kylebsmith/ESP32-S3-RLCD-cYbErDeCk/docs/DATUMS.md

# Dimensional datum sheet

Every dimension this enclosure is built from, with its provenance, its
corroboration, and its known weaknesses.

The rule is simple: **no number enters `cad/parameters.scad` without a source
that a third party can check.** Where a number could not be sourced it is listed
in [Open items](#open-items) rather than guessed, and the design is shaped so
that the gap cannot cause a part to clash.

| Tag | Meaning |
|---|---|
| `[VENDOR]` | published by the component manufacturer, in a drawing, CAD file or spec table |
| `[MEASURED]` | numerically recovered from a reference artefact by `tools/measure_reference.py` |
| `[DERIVED]` | arithmetic on a `[VENDOR]` or `[MEASURED]` value |
| `[STANDARD]` | an ISO/IEC standard or a manufacturer's fitting specification |
| `[DESIGN]` | a choice made by this project, with rationale |
| `[PROVISIONAL]` | not corroborated by a second independent source |

---

## Sources

| # | Source | Kind | Used for |
|---|---|---|---|
| S1 | `ESP32-S3-RLCD-4.2-3dFile.rar` — Creo STEP assembly, dimensioned DXF, dimensioned PDF, published by Waveshare at `files.waveshare.com/wiki/ESP32-S3-RLCD-4.2/` | Manufacturer CAD | All board geometry |
| S2 | `docs.waveshare.com/ESP32-S3-RLCD-4.2` and `waveshare.com/esp32-s3-rlcd-4.2.htm` | Manufacturer spec text | Panel type, resolution, connector types |
| S3 | `riitek.com/product/259.html` — "Mini Keyboard 518BT" | Manufacturer spec text | Keyboard outline and mass |
| S4 | FCC ID `YIZRT-RII518` (Shenzhen Riitek), granted 2011-05-23 | Regulatory filing | Keyboard identity, control/port faces |
| S5 | `github.com/nilseuropa/solar_term` — SolarTerm enclosure, two independent designs (`stl/ata/`, `stl/poc_*`) | Third-party reference artefact | Independent corroboration; keyboard pocket |
| S6 | `makerworld.com/models/3251467` — "SolarTerm: ShareWave ESP32 S3 RLCD4.2 Case", BY-NC-SA, derived from S5 | Third-party reference | Entry point; no geometry taken |
| S7 | ISO 273, ISO 4762, ISO 10642 | Standards | Fastener fits |

S5 is used as a **measuring instrument, not as a design**. See
[PROVENANCE.md](PROVENANCE.md).

---

## D-01 — Board mounting-hole pattern

**85.500 × 62.100 mm**, four positions, 3.50 mm inset from every PCB edge.

This is the single most load-bearing datum in the project: it fixes where the
board sits, and everything else is referenced to it. It is therefore established
three times, independently:

| Derivation | Method | Result |
|---|---|---|
| A | `stl/poc_bottom.stl` sectioned at Z = 0.05, four Ø2.700 bores | 62.100 × 85.500 |
| B | `stl/ata/Caseback.stl` sectioned at Y = −11.323, four Ø2.700 bores | 62.100 × 85.500 |
| C | Waveshare DXF `DIMENSION` entities #9 and #11 | 85.5 and 62.1 |

A and B are two unrelated enclosure designs by different authors. They agree
with each other to **0.001 mm** and with the factory drawing exactly.
`tools/measure_reference.py` re-derives A and B on every run and asserts the
cross-check; `tools/validate.py` asserts the value is not `[PROVISIONAL]`.

**The holes are not plain holes.** The PCB carries four Ø4.20 through-holes,
each with a surface-mount **SMTSO-M2.5-7ET** standoff on the back face: Ø5.50
body, 7.00 mm tall, female M2.5 thread. The enclosure drives M2.5 screws *into
the board's own standoffs*; it supplies no bosses of its own, and it must leave
the standoff seating plane clear.

## D-02 — Board outline

**92.50 × 69.10 × 1.60 mm**, R0.50 corners. `[VENDOR]` S1, drawing text
`92.5 PCB OD` / `69.1 PCB OD`.

See [C-01](#c-01--the-701-mm-figure-is-the-stand-base-not-the-pcb).

## D-03 — Board depth stack

All in Waveshare's `W` frame: `W = 0` at the PCB back (component) face,
`+W` toward the display.

| Feature | W | Note |
|---|---|---|
| Display glass front | +3.75 | what the front-face lip bears on |
| PCB front face | +1.60 | |
| PCB back face | 0.00 | datum |
| SMTSO standoff end | −7.00 | what the back plate bears on |
| 18650 holder end | −15.20 | the deepest feature on the board |

Clear depth the enclosure must provide: **10.75 mm** (+3.75 to −7.00).
Holder protrusion past the standoff plane: **8.20 mm** — this, not the cell
diameter, is what the battery cowl has to swallow.

## D-04 — Keyboard outline

**108.5 × 58.2 × 10.2 mm**, 75 g. `[VENDOR]`

Source: the manufacturer's own user manual, filed as the **User Manual exhibit
(attachment 1470433) of FCC ID YIZRT-RII518**, page 13, section
*6. Technical Specifications*:

> Dimension：108.5mmx58.2mmx10.2mm
> Weight：75g

This closes the ±2.54 mm rounding band the project carried for most of its life.
108.5 × 58.2 × 10.2 is 4.272 × 2.291 × 0.402 in, **every axis of which rounds
correctly to riitek.com's published `4.3*2.3*0.4in`** — so the vendor's inch
figure is a rounded restatement of this same value rather than a second
independent source.

**Why it stayed hidden.** The manual's text is converted to vector outlines —
the PDF title contains `转曲`, Chinese for *convert to curves*. `pdftotext`
returns 2 139 characters from the 14-page file, all of it FCC boilerplate; the
specification table has no text layer at all and appears only when the page is
rasterised. Any full-text search of these exhibits returns the confident, wrong
answer that they carry no dimensions — which is exactly what an earlier pass of
this project concluded.

### Corroborated by the manufacturer's own drawing

Riitek's current product page carries a dimensioned product-overview image which
prints **both units on every axis, in one string per dimension**:

> `108.5mm/4.3inch`   `58.2mm/2.3inch`   `10.2mm/0.4inch`

That is decisive on the direction of the conversion. 4.3 in is 109.22 mm, not
108.5, so the millimetre figure cannot be derived from the inch figure — the
inch figure must be derived from the millimetre one. The drawing also labels the
**mini-USB charging port** and the **power switch**, both on the same short
edge, and shows a 68-key field with no pointing device.

So two independent manufacturer documents twelve years apart — the 2011 FCC
manual and the current drawing — give the same outline to the digit. Whatever
changed between the 75 g and 64.8 g samples, **the outline did not.**

What is left is ordinary moulding tolerance. Neither document states one, so the
design assumes ±0.30 mm in plane and +0.40 / −0.00 mm on thickness, the latter
because the drawing does not say whether 10.2 mm is to the moulding's top face
or to the keycap crowns. Both are tagged `[DESIGN]` in `parameters.scad` rather
than dressed up as measurements.

### Traps, all confirmed from primary sources

- **109.22 × 58.42 × 10.16 is not a body.** It is this project's own round trip
  through 0.1-inch granularity — see [C-07](#corrections).
- **150 × 100 × 20 mm / 120 g is the retail box.** 38 % longer and 72 % wider
  than the certified body; the 120 g includes the cable and printed manual.
- **The Rii K18 is not this keyboard, and neither is the RT518/RT518S.** The
  RT518 manual gives 317.2 × 123.6 × 18.3 mm, 342 g — three times the length,
  with a touchpad.
- **`4.09 × 2.28 × 0.43 in` circulates widely.** Now traced: it is Amazon's own
  structured *Product Dimensions* field on ASIN B0B46F8RS6, which contradicts
  the *Keyboard Description* field on the same page (`4.3*2.3*0.4in`). Its
  length of 103.9 mm is physically impossible — all three measured third-party
  pockets are larger. Rii's own storefront ships the sentence *"Keyboard
  measures"* with the value **missing**, in both the rendered HTML and its
  JSON-LD; that empty slot is the likely thing a third party back-filled.
- **riimall.com's own storefront claims an integrated touchpad.** The FCC
  external and internal photographs show there is none. Marketing copy for this
  model is unreliable even from the brand's own shop.

## D-05 — Keyboard pocket

**109.85 × 59.15 × 11.0 mm** `[DESIGN]` — stated, not derived from the body plus a
clearance, so the envelope does not move every time a tolerance assumption is
revisited. What it must satisfy is asserted instead.

| Clears | per side, in plane | depth |
|---|---|---|
| nominal body 108.5 × 58.2 × 10.2 | 0.675 / 0.475 | +0.80 |
| body at tolerance 108.8 × 58.5 × 10.6 | 0.525 / 0.325 | +0.40 |
| ATA tray, a working device, 109.200 × 59.200 | +0.325 / −0.025 | — |
| grip case, measured, 109.406 × 59.005 | +0.222 / +0.073 | — |

The pocket was **110.2 × 59.4** until the front lip was checked with the
keyboard anywhere other than centred, and went negative at a corner — see
[O-09](#o-09--the-keyboard-lip-goes-negative-at-a-corner--closed). Tightening
it to the floor both assertions allow recovered about two thirds of that; the
rest came from **eight half-round locating ribs**, four on the long walls at
±X and four on the short walls at ±Y.

| | bare pocket | ribbed | largest body | smallest body |
|---|---|---|---|---|
| width | 109.85 | 108.95 | 108.80 → +0.075/side | 108.20 → ±0.375 travel |
| height | 59.15 | 58.65 | 58.50 → +0.075/side | 57.90 → ±0.375 travel |

Each rib is a cylinder centred **on** the wall plane, so half of it is buried
in material already there and only the inboard half is new — it fuses to the
wall with no seam to delaminate — and each is tapered over its first 1.6 mm at
the entry end, because the keyboard loads from behind. They are only 2*r wide,
so they clear both the service window and the corner blends easily. The ribs
are load-bearing for the lip guarantee, so `validate.py` measures the ribbed
span **from the rendered chassis** rather than trusting the parameters: a rib
that was specified and not built fails the lip check exactly as a bare pocket
does.

The height row against the ATA tray is **0.025 mm negative**, and that is
deliberate. The tray's own clearance over the 58.2 body is 0.50 per side; this
pocket's is 0.475. The 0.6 mm margin this design asserts against a working
reference is applied to the width, where the certified body is 108.5 and the
tray's 109.200 is the only physical evidence of what a real unit needs.

The depth sits **exactly** on its assertion at the top of the thickness band:
11.0 mm against 10.6 + 0.4. That is the one axis with no slack left, and it is
also the axis whose nominal is least certain.

Because this design's pocket is open front-to-back — the keyboard loads from
behind and is held forward by a pad on the back plate — there is no internal
floor-to-wall corner for a print fillet to interfere with, so the base relief
the ATA needs is not required here.

## D-06 — Board edge features

Positions relative to the mounting-pattern centre, which coincides with the PCB
centre at `(U, V) = (46.25, 34.55)`.

| Feature | Offset | Size | Source |
|---|---|---|---|
| Buttons ×3 (PWR/BOOT/KEY) | X = −10, 0, +10 | body 4.553 × 2.203 | `[VENDOR]` S1 |
| Microphones ×2 | X = **±32.500** | 4.00 × 3.00 × 1.00 | `[VENDOR]` S1 |
| 18650 holder | Y = **−19.400** | 77.80 × 22.10 | `[VENDOR]` S1 |
| Speaker grille | Y = **+16.000** | 14.70 × 10.45 | `[VENDOR]` S1 |
| USB-C | Y = 0.00, W = −1.170 | shell 9.582 × 4.163 | `[VENDOR]` S1 |
| microSD | Y = +19.15, W = −0.625 | socket 16.103 × 2.452 | `[VENDOR]` S1 |
| 2×8 expansion header | X = −0.10, Y = −0.70 | body 21.003 × 6.603 × 8.603 | `[VENDOR]` S1 |

**Independent confirmation.** Before S1 was located, three of these were
measured from S5 by sectioning `stl/ata/Caseback.stl` normal to the board's long
axis. They match the factory drawing exactly:

| Datum | Measured from S5 | Factory drawing S1 |
|---|---|---|
| Microphone offsets | ±32.500 | ±32.500 |
| Battery offset | −19.400 | −19.400 |
| Button pitch | 10.000 | 10.000 |
| Speaker grille height (4 slots × 3.05 pitch + 1.3) | 10.45 | 10.45 |
| microSD offset | +19.25 | +19.15 |

Two independent measurement paths converging to three decimal places is the
strongest evidence in this document.

## D-07 — Display

| Datum | Value | Source |
|---|---|---|
| TFT module outline | 91.00 ±0.10 × 67.60 ±0.10 × 1.50 | `[VENDOR]` S1 |
| Active area | **84.80 ±0.10 × 63.60 ±0.10** | `[VENDOR]` S1 |
| Pixel pitch | 0.2120 mm square, 400 × 300 | `[DERIVED]` |
| True diagonal | 106.00 mm = 4.173 in | `[DERIVED]` |
| Active-area offset from PCB centre | **−1.60 mm along U**, centred along V | `[VENDOR]` S1 |
| ... independently measured | −1.604 mm along U | `[MEASURED]` S5 `poc_top.stl` |
| Aperture used here | 86.8 × 65.6 | `[MEASURED]` S5 — a 1.00 mm reveal per side |

The offset is confirmed independently: the proof-of-concept enclosure's display
aperture centre sits at (34.5640, 45.6460) against a mounting-pattern centre of
(34.550, 47.250) — an offset of **−1.604 mm** along the same axis. That design's
aperture is also *exactly* 63.600 × 84.800, i.e. the active area itself with
zero reveal; the 1.00 mm per-side reveal used here comes from the later ATA
bezel and is the more forgiving of the two.

See [C-02](#c-02--the-active-area-is-not-42-inches-and-is-not-centred).

## D-08 — Reference enclosure, as-built

Measured from S5 for comparison, not used as design input.

| Datum | ATA design | Proof-of-concept |
|---|---|---|
| Outer envelope | 151.650 × 116.770 × 18.000 | 142.100 × 112.500 × 15.248 |
| Wall thickness | 2.900 | 1.000 |
| Board pocket | 71.116 × 94.519 × 13.000 | — |
| Keyboard tray | 59.200 × 109.200 × 11.400 | 60.600 × 110.498 × 10.750 |
| Back wall over the board | 3.000 | 3.500 |
| M3 insert bore | Ø4.000, 8.1 deep | — |
| Bezel | separate, 2.000 thick | separate top shell |
| Battery cover | separate, 83.0 × 27.0, 12.0 proud | — |

## D-09 — Acrylic display window

**70.8163 × 94.2193 mm**, ~1 mm chamfered corners, with a 1.0 × 29.3 mm relief
step on one long edge. `[MEASURED]` from `stl/ata/plexiglass.dxf`, a single
closed `LWPOLYLINE` of 26 vertices, DXF AC1015, `$INSUNITS = 4` (millimetres).

A 2D template is an exact, unambiguous statement of intent, so this is among the
highest-confidence datums available. It is carried as an optional part.

---

## Corrections

Recorded rather than quietly fixed, because each was believed and acted on
before being caught.

### C-01 — The 70.1 mm figure is the stand base, not the PCB

Early revisions carried `board_h = 70.1` from a distributor spec line, tagged
`[PROVISIONAL]`. The factory drawing shows that "92.5 × 70.1 × 13.5 mm"
conflates three different objects:

- **92.50** is the PCB length — correct;
- **70.10** is the moulded **stand base**, which overhangs the PCB by exactly
  1.00 mm on one long edge. The PCB is 69.10;
- **13.50** is the display-front-to-base-rear stack, and it **excludes the
  battery holder**, which protrudes a further 5.45 mm. Real maximum: 18.95.

A pocket cut to 70.1 leaves a 1 mm gap on one long edge. Consequence here: this
design discards the stand base and kickstand entirely, which removes the 70.1
dimension, saves 2.75 mm of thickness and 1.0 mm of width, and costs nothing
mechanically because the standoffs are on the PCB.

**The drawing can be read either way, and one reading is a trap.** Chaining the
hole offsets gives `4.50 + 62.10 + 3.50 = 70.10`, which appears to confirm the
70.1 figure — and a second, independent pass over the same drawing reached
exactly that conclusion. It is wrong: the 4.50 is dimensioned from the **stand
base** edge while the 3.50 is dimensioned from the **PCB** edge, so the chain
mixes two datums. Removing the base's 1.00 mm overhang gives the self-consistent
`3.50 + 62.10 + 3.50 = 69.10`, which matches the front view's own `69.1 PCB OD`
annotation and the 3.50 mm inset quoted on all four sides.

A third line settles it independently of the drawing: the reference enclosure's
board pocket is 71.1163 × 94.5193 against a bare PCB of 69.1098 × 92.5098 —
**1.0032 / 1.0047 mm per side, symmetric**. Against a 70.10 mm base the same
pocket gives a lopsided 1.01 / 0.508.

### C-02 — The active area is not 4.2 inches, and is not centred

An earlier revision derived the active area from the nominal "4.2 inch"
diagonal and a 400 × 300 matrix, giving 85.344 × 64.008 mm centred on the board.
The drawing gives **84.80 × 63.60** — about 0.5 mm smaller in each axis — and
the area sits **1.60 mm toward the U = 0 edge**, with margins of 2.25 mm and
5.45 mm rather than equal ones. The true diagonal is 4.173 in.

A frame cut to the derived figure would have been oversized *and* 1.6 mm off the
panel on one side. `tools/validate.py` now asserts both the value and the
offset.

### C-03 — The "expansion access window" was part of the carry hanger

A 24.004 × 29.382 mm tapered recess in `stl/ata/Caseback.stl` was recorded as a
`[MEASURED]` expansion-header window. It is not. It sits at board-relative
(X +45.2, Y +36.1) — diagonally off the corner of the PCB, largely outside the
board outline — and it is part of the reference's **carry hanger**, which is
precisely the feature that differs between its `Caseback.stl` and
`Caseback_left.stl` variants.

The window is now placed from S1 instead, at the header's real centre.

### C-04 — Waveshare's own header window is narrower than the header

Waveshare's stand base cuts 21.60 × 5.60 for a header whose insulator is
21.003 × **6.603**. Their window exposes the pin field, with the body sitting in
a wider recess behind it. This back plate is 3.2 mm thick and the header stands
8.603 mm off the PCB back — **1.60 mm proud of the standoff plane** — so the
body itself must pass through. The window here is sized from the body.

### C-40 — "It'll warp and float" — so the lip was tested warped

The v3 shell was reported against before it was printed: *"PLA warps and shit
over time so eventually it won't sit level and flush and it's not designed to
actually engage with the enclosure so it's just a floating slab on top."*

Half of that was wrong and half of it found a real defect.

**It did engage** — a continuous lip hooking the rim, 92.7 mm³ in one ring. But
the warp concern was right, and it was right about a mechanism the design had
not addressed at all.

### The inner face was a mating surface, and should not have been

The cover's whole inner face met the deck's whole front face. **Two large flat
surfaces meeting is exactly what rocks when either one bows**, and PLA bows —
on the bed, and again over months as it relaxes. The lip could be perfect and
the cover would still sit proud in the middle.

So the middle is not a mating surface any more. The inner face is recessed
0.50 mm across everything except a 5 mm perimeter land — which the wall
stiffens and keeps true — and four pads at the magnets, which stay at full
height because 0.5 mm of extra gap costs roughly half the pull.

**It floats over a void by design, rather than floating because it does not
fit.**

### Then the lip was deformed and asked again

A part that fits when perfect is not the question. The lip ring was displaced
under two failure modes and re-tested against the shell solid:

| | v3 as drawn | now |
|---|---|---|
| bow, corners lift 0.8 mm | 99.2 % held | **99.2 %** |
| splay, mouth opens 0.2 mm | **2.2 %** | 99.2 % |
| splay 0.3 mm | 0.0 % | **99.2 %** |
| splay 0.4 mm | 0.0 % | 37.8 % |
| bow 0.8 **and** splay 0.3 | — | **99.2 %** |

**Bow was never the problem** — the relieved face absorbs it completely. Splay
was, and the cause was the design's own arithmetic: **the hook is measured at
the mouth, but the land sits above it**, where the shell has already narrowed.
A 0.50 mm hook behind a 0.60 mm entry chamfer left **0.17 mm of real
engagement** — a third of the number it was being quoted as.

Cutting the entry to 0.20 and deepening the hook to 0.70 doubled the splay
tolerance, 0.17 → 0.35 mm. Every 0.1 mm of entry chamfer is 0.1 mm of
engagement given away.

### Two process failures worth recording

**A parameter edit silently did nothing.** The hook change was applied with an
unchecked string replacement that did not match, and the warp improvement was
reported from the *relief* change alone. It was caught by `git diff --stat`
showing **insertions and no deletions** on a patch that was supposed to replace
three lines. Parameter edits now assert the line they are replacing.

**A magic number failed the moment the design moved.** The interference check
carried a hand-picked 220 mm³ ceiling and rejected the deeper hook at 270.7.
The bound is now derived — rim length × hook depth × lip height = 359 mm³ —
so it tracks the design instead of freezing one version of it.

### Nothing outside the cover moved

Verified rather than asserted: the only changed parameters are `cover_*`, the
only changed module is `cover()`, and `check_golden --stl` reports chassis,
backplate and buttons identical to **0.00000 mm and 0.0000 mm³**.

### C-39 — The grip fingers were the wrong answer, correctly measured

C-38 replaced a warped flat plate with a tray on six sprung grip fingers. Every
number in it was good: six fingers biting 3.26 mm³ each, exactly even, zero
support. It was still wrong, and the owner's verdict named both halves — *"fingers
are gonna be fragile, visual aesthetic is of cheap consumer products."*

**Discrete snap features are a local answer to a global problem.** Each finger is
a small cantilever doing a job alone, so each is a place the part can break, and
six little hooks in a row read as moulded consumer plastic. Measuring them
evenly did not make them right. A mechanism had been bolted **onto** the object
instead of the object **being** the mechanism.

### The rim was already an undercut

Measured on the rendered chassis, the flank tapers **1.023 mm per side over the
last 3.60 mm** before the front face:

| depth below the face | half-width | undercut |
|---|---|---|
| 0.05 | 56.928 | — |
| 2.00 | 57.390 | 0.462 |
| 3.60 | 57.951 | **1.023** |
| 5.00 | 58.125 | 1.197 |

So a single continuous eased lip hooks that rim **all the way round at once** —
roughly 460 mm of engagement instead of six 9 mm fingers. Nothing local, nothing
sprung, nothing to snap off. It goes on in one press: the lip rides a 1.5 mm
ramp of the deck's own taper while the whole shell breathes a few tenths, and
the four magnets — **unchanged, same sites, same pockets** — pull the last of it
home.

Measured: **92.7 mm³ of interference in exactly one region.** One ring, not six
bites.

### Depth was set by the ports, not by preference

The USB-C opening's top edge is at chassis z = 12.78, so a wall deeper than
**4.07 mm** starts covering it. 3.60 leaves 0.47 mm of clearance and still buys
the full 1.023 mm undercut. The lip takes 0.50 of that — half — so the ramp
stays gentle and the shell is never forced.

### Two overhangs the measurement caught

The lip's flare was built at 1:1, which is 45° on the straight runs but measured
**40.2° at the corners**, where the superellipse takes a smaller radial step for
the same rise. And the shell inherited the deck's own edge roll, which flares
outward off the bed at ~42°.

Raising the flare to 1.35:1 and giving the cover its own longer roll
(`cover_edge_soft` 0.80, `cover_edge_roll` 0.24) took support from **85.3 mm² to
0.00**. An intermediate attempt at 1.75:1 made it *worse* — 372 mm² — because it
left only 0.61 mm of chamber; recorded because the obvious direction was the
wrong one.

### The checks

`MAGNET` now asks about the **ring**, and the load-bearing one is that it *is* a
ring: **more than one engagement region means the retention has gone local again
without anyone deciding that it should.**

### C-38 — The cover was a flat plate, and flat plates warp

The first cover was a 116 × 140 mm plate, 2.95 mm thick, held on four magnets.
It printed warped, and a warped plate cannot register on a flat face. Reported
from the print: *"it prints unflat so it doesn't actually clasp."*

Nothing was dimensionally wrong with it. It is the **geometry itself** that is
the defect — a thin wide plate is exactly what curls on an FDM bed, and this
design then asked four discrete magnets to pull that curl flat across a
520 mm perimeter. They cannot. The plate and its retention were both wrong for
the same reason: **the design registered on the face, and the face is the part
that moves.**

### One fix for both halves

A closed perimeter skirt turns the part from a plate into a shallow box
section, which barely warps to begin with, and moves registration from the
face to the **sides**, which do not.

**The shell was already the right shape for this.** Measured on the rendered
chassis, it is a barrel: full 116.250 mm from z = 4.90 to z = 11.90, tapering
to 113.914 at the front face. That is **1.168 mm per side of lead-in that
already existed**, and a full-width band to grip. No enclosure change — the
geometry was frozen, and it did not need to move.

| | Was | Now |
|---|---|---|
| Form | flat plate | tray, 8.00 mm skirt |
| Registers on | the front face | the shell's flanks |
| Retention | 4 magnets | 6 grip fingers + the same 4 magnets |
| Magnets | structure | seating and anti-rattle |
| Shear | `cover_reg_depth` platforms in the apertures | the skirt |

The magnet configuration is **unchanged** — same four sites, same pockets, same
gap.

### Three things the measurements caught

**Fingers, not a continuous band.** A continuous interference lip would have to
be stretched by hoop strain over 116 mm of stiff wall. PLA-CF cracks before it
stretches. Discrete cantilevers flex locally — and because each finds its own
position, **residual warp costs nothing, since no finger depends on another
being where it should be.** Root strain is `3δt/2L²` = **0.94 %** at δ = 0.25,
t = 1.60, L = 8.00. That is also why the skirt is 8 mm and not 5: strain goes
as 1/L², and at 5 mm it is over PLA-CF's limit.

**A finger on the corner gripped a quarter of its neighbours.** The first
placement put one at y = 62, past where the corner blend starts at y = 58.9 and
the shell begins to narrow. Measured interference: **2.68 and 1.21 mm³ against
5.08** for the others. A presence check would have passed it. The fix was to
stop sharing positions between the flanks — they do not have the same
obstructions, since +X carries the USB-C and microSD tunnels and −X the
keyboard service window. All six now bite **3.26 mm³ each, exactly even.**

**An unsupported ledge, 1,200 mm² of it.** The plate was an `rse_soft` barrel
and the skirt a separate straight tube; where they met, the skirt stood proud
of the plate's inset bottom, leaving an annular overhang facing the bed. One
continuous straight-sided form removes it, holds the wall constant, and is the
more minimal object. Printed show-face-down the part now needs **0.00 mm² of
support**.

### The checks

`MAGNET` loses the two register-platform checks and gains three that ask the
mesh: that the skirt lands inside the full-width band, that every finger bites,
and — the one that would have caught the corner — **that they bite evenly**.

### C-37 — The flood-coat dam was lying on two countersinks

The back is finished with poured self-levelling acrylic, which needs a wall to
level against. The obvious move is a dam around the plate's perimeter, and that
is what was built: 1.20 mm high, 2.00 mm wall, following the plate outline.

The audit rejected it immediately — **6 probes covered, up to 1.20 mm of
material over the countersink**, on both M2.5 board screws at y = +62.83. That
is [C-25](#c-25--the-cowl-was-lying-on-top-of-two-screws-and-a-window) again,
exactly: a feature lying on top of a screw, dimensionally perfect and
functionally impossible.

**There is no ring that works.** The dam has to clear four M2.5 countersinks
*and* the 82.80 mm battery cowl, on a 109.25 mm plate:

| Constraint | Dam outer edge must be inboard of |
|---|---|
| Board screw heads at x = ±42.75 | x = 40.25 → 14.375 mm inset |
| Board screw heads at y = +62.83 | y = 60.33 → 6.295 mm inset |
| Battery cowl, 82.80 wide | x = 41.40 |

A 14.4 mm inset leaves a flooded panel 76 mm wide — narrower than the cowl that
crosses it. The geometry does not close.

And the functional objection is worse than the geometric one: **a coat poured
over the fasteners seals the plate shut.** The dam would have made the device
harder to open, which is the opposite of the requirement it was serving.

### The fix: the dam is a jig, not a feature

The plate drops into a frame that stands `pour_dam_rise` proud of it, the resin
levels inside that, and the frame comes off once the coat has gelled.

It surrounds the plate rather than crossing it, so it is outboard of every
fastener by construction and cannot foul anything. It touches no validated
geometry. It is reusable, and it can be reprinted without reprinting a part of
the device.

The general lesson: **a fixture is not a worse answer than a feature, it is
often the correct one.** The requirement was "the resin must have something to
level against during the pour" — which is a statement about a *process*, and
the instinct to solve it in the *product* is what put material over a screw.

### C-36 — The battery cowl gained a millimetre, and the golden check caught it

Not a defect. A deliberate change, recorded because `tools/check_golden.py`
refused it and refusing it is the check working exactly as designed.

The cowl is not only a cover for the cell. Resting on it the deck **leans
toward the user**, which is the posture it is used in on a desk, and it is what
the fingers wrap when it is held. Both wanted more of it.

| | Was | Now |
|---|---|---|
| `batt_cowl_extra` | — | **1.00** |
| `batt_cowl_rise` | 10.00 | **11.00** |
| `batt_cowl_crown` | 0.700 | **0.622** |
| Lean angle on the cowl | 6.38° | **7.01°** |

7° sits inside the 5–11° band keyboards are normally tilted to.

**`batt_cowl_crown` moved on its own, and that is correct.** It is
`(cell clearance) / (rise - wall)`. The numerator — what the cell actually
needs — is unchanged at 5.60 mm. Only the denominator grew, so the crown starts
proportionally lower and **the extra millimetre goes into the dome rather than
into the cavity**. The cell's clearance is preserved exactly while the form
gets fuller, which is what a hand rest wants. Had the numerator moved, this
would have been a defect.

**Why the golden baseline was re-cut rather than the change gated.** `batt_cowl_*`
is not in `check_golden.py`'s `V2_ONLY` list, so the change reaches v1's frozen
surface. That list exists for parameters that *cannot* move v1 geometry; this
one does, and pretending otherwise by widening the list would have made the
check lie. The alternative — gating on `variant` — does not work either, because
`check_golden` parses `parameters.scad` as written rather than forcing
`variant = 1`, so a gated value would still read as changed. That is a latent
weakness in the tool and is recorded here as such.

So the baseline was re-cut with `--update`, which is the sanctioned path for a
deliberate change. The check did its job: this did not happen silently, it
happened in front of somebody who then had to write this down.

**The already-printed chassis is unaffected.** The cowl is on the back plate,
which is a separate part with unchanged mounting. Reprint the plate; keep
everything else.

### C-35 — The crush ribs were narrower than the nozzle that had to print them

Eight ribs, 0.35 mm tall, cut into the magnet bore so the discs would grip
across their own 0.20 mm tolerance band. The heights were right, the
interference arithmetic was right, and the ribs could not be printed.

The rib was formed by subtracting a cylinder of radius `magnet_rib_h` centred
**on** the bore wall, which leaves a bump exactly `2 × magnet_rib_h` wide at
its base — **0.70 mm**. Against the 0.80 mm nozzle this design was re-derived
for in [C-33](#c-33--every-wall-was-measured-against-the-wrong-nozzle), that is
**0.87 of a single extrusion.** A feature narrower than one bead is not a
feature; the slicer renders it as whatever the bead happens to do there. None
of the designed 0.10–0.30 mm of interference was under this file's control.

**Why nothing caught it.** Every magnet check asked about a *diameter* — bore
against disc, skin thickness, seat depth, whether the pocket was reachable.
The defect is a *width*, and no check in the suite had ever measured one.
C-33 re-derived every **wall** against the new nozzle and stopped there,
because a rib is not a wall.

### The fix

The height is correct and stays. The base widens to two clean extrusions, and
both the cutter radius and its offset are now **solved** from the height and
the width rather than being implied by a single number doing two jobs:

| | Was | Now |
|---|---|---|
| `magnet_rib_w` | 0.70 (implied) | **1.60** = `2 × nozzle` |
| `magnet_rib_n` | 8 | **6** |
| cutter radius | 0.35 | **1.5004** (derived) |
| cutter centre from axis | 2.75 (on the wall) | **3.9004** (derived) |
| `magnet_rib_h` | 0.35 | 0.35 — unchanged |

Given bore radius *R*, rib height *h* and base width *w*, the bump is the part
of the bore left uncut by a circle of radius *r* centred at distance *c*. Its
innermost point must sit at *R − h* and its base must meet the wall at ±*w*/2,
and those two conditions fix both:

```
y = w/2                    x = sqrt(R² − y²)
a = x − (R − h)            r = (a² + y²) / 2a          c = r + (R − h)
```

**The count had to move too, and for two independent reasons.** At 1.60 mm
wide, eight ribs leave gaps of **0.56 mm** — below one extrusion, so the
slicer bridges them and the ring prints solid with no crush relief anywhere.
Worse, the *cutters themselves* overlap at eight: their centres sit 2.985 mm
apart against 3.001 mm of summed radius, so the ribs are malformed in the
model before slicing is even reached. Six leaves 1.28 mm gaps and 0.90 mm of
cutter clearance.

### Measured on the rendered mesh

| | Before | After |
|---|---|---|
| Rib base width | 0.70 mm — **0.87 extrusions** | 1.45 mm — **1.82 extrusions** |
| Gap between ribs | 1.46 mm | 1.40 mm |
| Rib height | 0.35 | 0.374 |
| Bore closes to | Ø4.80 | Ø4.777 |
| Lobes counted | 8 | **6** |

Measured across 88 ribbed sections through both magnet stations. Rib height
and tip diameter read very slightly proud of nominal because the section
samples the circumradius of a `$fn = 64` facet; the bias is under 0.03 mm and
is conservative — it reports marginally *more* interference than is drawn, not
less.

Against the disc's own band this leaves 0.12 mm of diametral interference on
the smallest disc (Ø4.90) and 0.32 mm on the largest (Ø5.10), which is what
six deforming ribs are for.

### The check

`MAGNET` gains two checks that measure the rib and the gap beside it **on the
mesh, in extrusions** — the first checks in the suite to interrogate a feature
width rather than a diameter. Three asserts in `parameters.scad` refuse the
same mistakes at parse time: a rib under one extrusion, gaps under one
extrusion, and cutters that overlap each other.

The general lesson is the one this file keeps recording. C-33 asked *"is every
wall thick enough for this nozzle?"* and answered it completely. It did not
ask *"is every **feature** wide enough for this nozzle?"*, and a rib, a web, a
gusset tip and a slot land outside the first question.

### C-34 — The board is a perfect rectangle, and the pocket assumed a radius

The drawing gives the PCB R0.5 corners. **The board in hand is square at all
four.** Same class of error as the 18650 holder (C-21): a vendor radius the real
part does not have.

It mattered because a rounded pocket only accepts a square part while

    r <= c * sqrt(2) / (sqrt(2) - 1)

and the pocket was modelled at R2.0. Worse, `board_pocket_w` was built on the
drawing's 92.50 while the owner's board measures **92.70**, so c was 0.400 in X,
not the 0.500 it claimed — which caps r at 1.37. The arc left material
**0.193 mm** inside where the board's corner had to go and it would not slide in.

Fixed at the datum, not with a workaround: the pocket is sized on
`max(drawing, measured)` with `board_fit` = 0.60 per side, and the radius is
1.20. A square 92.70 × 69.10 board now clears everywhere with 0.351 mm at the
corners. Corner reliefs were tried first and are worse here — a circle at each
theoretical corner reaches x = 48.55 and the lower fastener bosses start at
47.94, so it chewed into them.

Three degeneracies surfaced with it, all the same shape — two cutters meeting on
exactly the same plane: the groove against the back opening's edge, and the
keyboard bay's wall against it at exactly z = back_t. Both now overlap by 0.2–0.4
mm. `rbox` also rendered a hull of four zero-radius cylinders, which is not a
solid, so it takes a square box when r <= 0.

### C-33 — Every wall was measured against the wrong nozzle

The deck prints on a **0.8 mm nozzle**, and `nozzle` said 0.4. That is not a
slicer setting: a wall that was three comfortable beads at 0.4 is 1.2 at 0.8,
which the slicer lays down as one bead with a gap beside it. Measured on the
printed part, against a floor of two beads (1.60 mm):

| | was | now |
|---|---|---|
| tongue groove, outboard wall | 0.96 | **2.14** |
| speaker grille webs | 1.11 | **2.83** |
| microphone slot | 5.4 × 2.5 | **8.0 × 3.2** |

The groove could not be fixed by depth or by the roll: at `wall` = 3.2 the edge
roll withdraws the outer face by 0.94 mm exactly where the groove sits, so the
wall itself was the variable. `bottom_wall` is now `wall + 1.2`, which also
means the back opening and the plate are **not centred on the part** — cutting
them symmetrically ate 1.2 mm of the thicker wall and took the groove's entire
lower lip with it, so the tongue was captured by nothing at all.

Two asserts were also moving their own goal posts: `wall - edge_soft >= 5 *
nozzle` and `cowl wall >= 4 * nozzle` were 2.00 and 1.60 mm at a 0.4 nozzle and
silently became demands for 4.00 and 3.20 when it changed. Both are stated as
lengths now.

`validate.py` gained a `MIN WALL` class that sweeps sections and reports the
closest approach between any two boundaries in each part — which is what found
the grille webs and the magnet shaft against the microSD tunnel, neither of
which any named check was looking at.

### C-32 — The plate's bed face was a pad over open air

`docs/ASSEMBLY.md` prints the back plate **cowl up**, so its inner face is the
bed face. That face was not flat: the 0.25 mm keyboard keeper stood proud of it,
so the pad's **6233 mm²** was the only thing touching the bed and the remaining
**5777 mm² — 48% of the underside —** printed as a flat sheet over 0.25 mm of
open air.

The keeper's *thickness* was right and derived (`board_depth − kbd_depth`); the
wrong part was which of the two parts carried it. The chassis's keyboard bay now
stops 0.25 mm short of the front panel, leaving a band the keyboard bears on,
and the aperture is carried down through that band at the same section as the
flared aperture's narrow end so the two meet tangentially. The plate's inner
face is one plane at z = 3.20 with **11,888 mm² flat on the bed** and 166 mm²
within a millimetre of it. Nothing about the keyboard's clear depth, bearing
area or retaining lip changes.

### C-31 — Two countersinks were breaking out through the plate's rim — BLOCKING

The upper pair of shell-screw countersinks was positioned at
`plate_half_h − head/2 − margin`. `plate_half_h` is the plate's **mid-thickness**
section, and the outer *face* is rolled in from it by `plate_edge_soft`. Worse,
`boss_cx` = 51.24 lands inside the face's corner blend, which starts at
x = 48.63 — and there the outline runs diagonally, so a vertical extent is not a
clearance. The Ø4.0 countersink had **0.022 mm** of plate to bite on and opened
a notch in the rim at both top corners.

The give-away is topological, not dimensional: a countersink that has merged
with the outline is no longer an interior ring. `validate.py` now checks exactly
that, and it is also why the first attempt at a fix went wrong — measuring the
"highest usable y" against the *rendered* plate returns 58.5, because the
outline being measured already contains the breakout. Solved against the
analytic face outline instead: **62.25**, which also clears the microSD tunnel's
61.425 floor by 0.825 mm.

`boss_cx` cannot move inboard to escape the blend: the board pocket floors it at
50.05 and the blend starts at 48.63.

### C-30 — The tongue groove's wall was 0.48 mm, and three places said 1.60

`back_t − tongue_depth` is not the wall left outboard of the groove. That
arithmetic assumes the outer face sits at the nominal envelope; `rse_soft`'s edge
roll withdraws it by up to 1.2 mm over the back 4.7 mm of the thickness, and the
groove sat inside that band. The rendered chassis carried **0.480 mm** — 1.2
extrusions — while the source comment, the documentation and
`validate.py`'s own "groove leaves a printable bottom wall" check all said 1.60.
All three computed from parameters; none touched the mesh.

`tongue_depth` 1.6 → 1.3, `tongue_z` `back_t/2` → 2.2, and `tongue_len` gains
`fit_slide` so shortening the groove does not shorten the tongue. Measured
result: **0.943 mm** (2.36 extrusions), engagement unchanged at 0.90 mm, tongue
tip unmoved. The check now ray-casts the rendered chassis and reports both the
measurement and what the old arithmetic claimed.

### C-29 — The button cap was the reference sprue's bounding box

`button_cap_w/h` were 5.2 × 4.0, taken as the reference cap's cross-section.
They are its **bounding box**: 5.2 is the flange skirt at the rear face and 4.0
is the sprue's axial depth. The cap's own prismatic section is a constant
4.800 × 3.800 swept along the cap axis.

At 5.2 in a 5.400 aperture the caps had **0.10 mm per side** against this
project's own sliding fit of `fit_slide` = 0.30 — they would have bound.
`button_flange` was wrong in the same way: 0.4 was the past-*aperture* figure
used as a past-*cap* one, leaving 0.200 of overhang against 0.200 of float, so a
cap could walk out of its own aperture. Now 4.8 × 3.8 with a 0.7 flange:
0.30 mm per side of clearance, 0.40 mm per side of overhang.

### C-28 — The fix for C-25 opened a slit into the battery cavity — BLOCKING

C-25 found the battery cowl lying on top of two M2.5 board-screw countersinks
and fixed it two ways at once: by deriving the cowl's plan form (82.80 × 27.10)
and by opening its outer plan corner from **6.0 to 12.6** to pull the flank off
the screws.

The second half of that fix was itself blocking. A fuller outer corner draws the
surface **in** at 45°, while the cavity's near-square R2.2 corner stays where it
is. The wall between them went from 2.07 mm on the flats to **0.0385 mm at the
corner** — an open slit into the 18650 cavity, roughly 0.6 mm of arc by 3.8 mm
tall, on all four corners. The part was watertight and printed as a single body,
so nothing downstream objected.

| | flats | corner |
|---|---|---|
| declared `batt_cowl_wall` | 2.00 | 2.00 |
| at `batt_cowl_base_r` 12.6 | 2.07 | **0.0385** |
| at `batt_cowl_base_r` 6.0 | 2.07 | **1.0246** |

**Why nothing caught it.** Four assertions guard this cowl. Three are
one-dimensional — `rse_x_at()` horizontal extents — and the fourth measures the
cavity against the **holder**. Not one of them measures the outer surface
against the cavity, which is the only pair of surfaces that defines a wall. The
`OBSTRUCTION` class added in C-25 has the same blind spot: it asks what lies
*over* a hole, never how thin something got beside one. This is the project's
recurring failure in its purest form — *every defect found has been in geometry
no check interrogated*, and the corner is where one-dimensional checks go blind.

**Why no single corner radius fixes both.** The holder's square corner is at
(38.90, 11.05) and the screw axis at (42.75, 11.65) — 3.896 mm apart. Less the
Ø5.0 head radius, 1.396 mm remains for clearance *and* wall, against the
0.50 + 2.00 = 2.50 the design asks for. Every value of `batt_cowl_base_r` trades
about a millimetre of screw clearance for about a millimetre of corner wall and
the sum never exceeds ~1.1 mm.

**Resolved by decoupling them.** The corner goes back to 6.0, and the two lower
screws get their own Ø5.2 relief bores straight through the cowl — local access
instead of reshaping the whole shell to reach around. The bores live entirely at
z < 0, so nothing in the plate is touched, and they leave a 1.02 mm web to the
cavity.

`validate.py` gained a `COWL` class that reads the wall off the rendered plate
as a **distance** between the outer ring and the cavity ring, at every height —
not as an extent — and re-probes a Ø5.0 driver column to both screws.

**This defect shipped.** It was present in `v1.0` (`6a9ded1`) and in the STLs
issued from it. `v1.1` is the first release without it.

### C-27 — The back plate's stiffening ribs were not there

`backplate()` added three 3.0 mm ribs across the keyboard bay, with a comment
saying they "run in the plate's weakest direction: the long span between the
bottom tongue and the spine". They contributed **nothing**.

`cube(..., center = true)` centres in Z as well as X and Y — the same reading
error as C-14's tongue and groove. At a z-centre of
`back_t + kbd_keeper_t/2 - 0.01` and a height of `kbd_keeper_t` they occupied
z 3.19…3.44, entirely inside the keeper pad at z 3.19…3.45. Sectioning the
rendered plate at z = 3.30 and z = 3.44 gives 6275.2 and 6280.2 mm², identical
to a bare pad, and deleting the ribs changes the part's volume by
**0.000000 mm³**.

Nor could they have worked as written: `kbd_keeper_t` is
`board_depth - kbd_depth` = **0.25 mm**, so any rib standing proud of the pad
would be a fraction of a millimetre tall and would come out of the keyboard's
0.40 mm of float. Deleted rather than rescued. `tools/structure.py` measures
section properties from the mesh, so none of its published figures move.

This one was harmless — it wasted no filament and trapped nothing. It is
recorded because a feature that claims structure it does not provide is how a
design stops being checkable.

### C-25 — The cowl was lying on top of two screws and a window

Every check in the suite asked whether a hole had been **cut**. None asked
whether anything was **lying on it**. Both classes of defect below passed 76
checks, and both are the same mistake: the battery cowl's plan form was copied
from the reference's separate clip-on cover — which sits on a blank panel — and
this cowl is integral to a back plate that is already crowded.

`batt_cowl_w/h` were 83.0 × 30.0 and `batt_cowl_foot` was 3.2. `blend` in
`rse_blob()` is an outward offset of the **whole section**, so the cowl's
footprint **at the panel** was 89.4 × 36.4, not 83 × 30. It covered:

| Feature | Position | What was over it |
|---|---|---|
| lower M2.5 board screws | (±42.75, +0.25) | **1.11 mm** of cowl foot across the whole Ø5.0 countersink — measured 17/17 probes blocked |
| expansion-header window | y 26.50 … 34.70 | **3.60 mm** of its 8.20 mm height, up to **5.84 mm** deep; clear mouth 4.70 mm against a 6.60 mm header body |

Consequence: two of the four screws that carry the board and the cell could not
be inserted at all, and the expansion header could not be mated. Measured by
ray-casting along +Z through the rendered plate, which is the method the fix is
asserted with.

**The geometry is over-constrained and no single number fixes it.** The holder
is 77.80 wide and the countersink rim reaches x = 40.25, leaving 1.35 mm for a
clearance plus a wall that together need at least 1.9 — so the cowl *must*
overlap the screws in plan unless its corner retreats off them. The resolution
is four coupled changes, all now derived rather than chosen:

- **`batt_cowl_w/h` derived** from `batt_bay_w/h + 2*(clear + wall)`:
  82.80 × 27.10 instead of 83.0 × 30.0. The height was the accidental part —
  the cavity had 1.95 mm per side over the holder in V where the design's own
  declared `batt_cowl_clear` is 0.50. It is now 0.50, as declared.
- **`batt_cowl_foot` 3.2 → 0.6.** It was never a tangent fillet: 3.2 mm of
  flare decayed over `foot_f` = 0.20 of a 10 mm rise, i.e. 2.0 mm of height.
  The bound is the expansion window's lower edge.
- **`batt_cowl_base_r` 6.0 → 12.6.** This is what pulls the cowl's lower flank
  off the screws: on an R6 corner the footprint still reaches x = 41.61 at
  y = +0.25, which is 1.36 mm inside the countersink. At 12.6 it reaches 39.36
  and clears the rim by 0.89 mm.
- **`batt_cowl_base_ri` 3.0 → 2.2.** Shrinking the cavity re-opened the
  `board_pocket_r` trap: at 3.0 the holder's square corner at (38.90, 11.05)
  fell 0.98 **outside** the cavity outline. At 2.2 it is 0.88 inside.

`batt_cowl_crown` was wrong at the same time and for an unrelated reason — see
[C-26](#c-26--the-crown-started-a-millimetre-above-the-holder).

New check class **OBSTRUCTION** in `tools/validate.py` now probes every
fastener head footprint and every window in the plate along its access axis.
New check class **STACK** measures the cowl cavity as a *section* at the
holder's deepest plane rather than as a depth.

### C-26 — The crown started a millimetre above the holder

`batt_cowl_crown` was 0.50 with a comment that already stated the right rule —
"the sides must stay parallel until they are clear of it". They did not. The
holder reaches `batt_protrusion - back_t` = 5.00 mm below the panel and the
cavity's rise is 8.00, so 0.50 began the crown at 4.00 mm, a **millimetre too
early**. Measured on the rendered plate the cavity closed to **77.592 mm** at
the holder's deepest plane against a **77.80 mm** holder — 0.104 mm of
interference per side, which is also the 0.17 mm³ that the clash test reported
and passed, because its threshold is 1.0 mm³ for mesh-faceting noise.

The check that covered it was one-dimensional: *"the cell reaches z = −5.00,
the cowl inner face is at z = −8.00, clearance 3.00 mm"*. That is a depth. The
crown closes the **section**, and a depth cannot see a section.

`batt_cowl_crown` is now derived from the holder's own protrusion. Measured
after the fix, the cavity holds 78.800 × 23.100 at every height down to the
holder's deepest plane: +0.500 mm per side in both axes, exactly the declared
`batt_cowl_clear`, and the board-to-plate clash volume went from 0.17 mm³
to 0.00.

### C-24 — Nothing held the keyboard, and the front lip went negative at a corner

The keyboard is a drop-in part. Nothing bonds or clamps it in X or Y — it is
held only by the front lip and the keeper pad behind it. So where it sits is
not a worst case on paper; it is wherever it lands.

With a bare pocket at 110.20 × 59.40, a minimum-tolerance body had **1.00 mm
of travel in X** against a front lip of only **0.85 mm per side**. Slid hard
over, the aperture edge cleared the keyboard by 0.05 mm on the long side and
went **0.36 mm negative at a corner** — a visible sliver of aperture opening
into the pocket.

A one-dimensional check could not see it. Measuring the lip at the mid-span of
each edge reports a healthy lip on all four sides; the failure is diagonal,
where the pocket's corner radius and the aperture's corner radius approach each
other. That is this design's recurring defect class — the same shape of error
as [C-05](#c-05--corner-radii-that-bite) and
[C-08](#c-08--a-guessed-corner-radius-hid-a-defect-that-a-1-d-check-could-not-see).

Two coupled changes, because tightening alone could not fix it: the pocket went
to the floor both asserts allow, and the remaining play was taken out
mechanically.

| Parameter | Was | Now | Floor |
|---|---|---|---|
| `kbd_pocket_w` | 110.20 | **109.85** | 109.80 |
| `kbd_pocket_h` | 59.40 | **59.15** | 59.10 |
| `kbd_locating_ribs()` | absent | **8 ribs, 4 pairs** | — |

The ribs are unioned *after* the pocket difference closes, so they are added
material rather than a surviving remnant of a cut. Worst-corner lip is now
**+0.383 mm**, measured on the rendered mesh rather than computed from
parameters.

Confirmed on the printed part: the keyboard fits with no play and no sliver.

### C-23 — The button flange had nowhere to live behind the wall

The space behind the top wall belongs to the board, and the button design had
been quietly spending it twice.

A full-thickness flange sitting behind the wall fouled the board. Cutting it
back to a bare 0.40 mm flange cleared the board but left the caps **0.34 mm
short of ever touching a switch** — a button that could not be pressed. Neither
variant could be made to work, and the reason is structural rather than
numerical: both were trying to find travel in clearance that another part
already owns.

The resolution is that the flange does not live behind the wall at all. It
lives **in** it, in a counterbore cut from the wall's inner face, and only the
plunger passes through. Travel is then bought from the wall's own thickness
instead of from the board's clearance, which is the one budget nothing else is
claiming.

```
btn_cb_depth = 1.00   // flange counterbore, from the wall's inner face
btn_flange_t = 0.40   // flange thickness
btn_travel   = 0.60   // [DERIVED] the difference - free travel
```

The stack that results, from the cap tip inward:

| z (mm) | What is there |
|---|---|
| 0.00 | cap tip, 0.6 proud of the dish floor |
| 0.60 | dish floor |
| 2.90 | the top wall's inner face |
| 3.44 | the plunger's face, `btn_reach` behind it |
| 3.49 … 3.69 | where the actuator actually is, once the board's ±0.10 mm mounting float is allowed for |

The 0.50 mm the board leaves behind the wall stays free for the plunger and for
travel, which is what makes the press reach the switch across the whole float
range rather than only at nominal.

### C-22 — The service window was cut on both flanks, and the one that mattered missed the switch

Two defects in one feature, and the second was caused by the first.

The 518BT's power slide switch and its charging port share one short edge, so
without a window through the flank the deck cannot be switched on at all. An
earlier version cut a window on **both** flanks, justified in the source as
"so the keyboard can go in either way round" — which it cannot. The keys only
read one way up. The second window was reaching nothing, on a wall that had
been opened for it.

The expensive part was the consequence. The pair was generated by mirroring
about the bay centreline rather than by positioning each window against the
features it serves. Measured on the owner's unit, the slide switch starts
**10.4 mm** from the keyboard's top edge and the USB-C receptacle **29.6 mm**,
so everything that matters lies in a band roughly 10.4 … 38.6 mm down one short
edge. The mirror put the left-hand window — the only one that reaches anything
— at **15.4 … 49.4 mm**, a full **5 mm clear of the slide switch it exists to
reach**. The window was present, correctly sized, cleanly cut, and useless.

A symmetric feature had been trusted because it looked deliberate. Mirroring is
not a substitute for positioning: it preserves the shape of a feature while
discarding the datum that gave it meaning.

Now one window, on the **left as the device is used** (`sx = -1` in this
frame, where +X is right looking at the front face), positioned from the
keyboard's **top** edge rather than from the bay centre, spanning **8.2 …
41.8 mm** so it clears both features with margin on either side — and clears
either connector revision, the owner's Type-C unit and the mini-USB one on the
factory drawing alike (see [C-20](#c-20--there-are-two-keyboard-revisions-and-the-corner-is-not-an-arc)).

```openscad
kbd_access_cy = kbd_top_edge - kbd_access_from_edge - kbd_access_w/2;
for (sx = (kbd_access_both_sides ? [-1, 1] : [-1]))
```

`kbd_access_both_sides` remains as a parameter rather than being deleted, so
the decision stays visible and reversible instead of becoming an unexplained
asymmetry in the model.

### C-21 — Three values whose stated reasons were wrong

All three survived adversarial refutation in the re-derivation pass. Two keep
their value and lose their justification; one moves.

- **`expansion_body_h` 8.603 → 8.700.** 8.603 is the header component's own
  bounding-box height. Waveshare's assembly seats it insulator 8.500 + 0.100
  lead + 0.100 seating below the PCB back plane. **The bbox of a part in
  isolation is not where the assembly puts it** — and the dependent figure,
  how far it stands proud of the standoff plane, was 1.60 and is 1.70.
- **`batt_cowl_base_ri` stayed 3.0, for a different reason** (it is now 2.2 —
  see [C-25](#c-25--the-cowl-was-lying-on-top-of-two-screws-and-a-window)). It was justified
  by "the holder's corners are R2.0". They are not: in the STEP the holder's
  plan form is exactly square at every height through the body — 0.0000 mm
  deviation from its bounding rectangle, 504 of 576 edges straight, every
  circle in the part on the cell axis. The real constraint is that a cavity
  corner must not bite into a square-cornered body inside it.
- **C-11's replica tangency figures.** "6.99 (tangency 6.81 / 6.88)" is a fit
  artefact; on the replica's authored vertex ring at z = 7.000 each flat is a
  single segment, so the tangent points are **exact** and the figure is
  7.000 / 7.000.

### C-20 — There are two keyboard revisions, and the corner is not an arc

**The charge port.** The owner's unit is **Type-C**. The drawing this project
works from labels "USB Charging Port" and draws a mini-USB connector. Both
sheets are otherwise identical — same layout, same `108.5mm/4.3inch`,
`58.2mm/2.3inch`, `10.2mm/0.4inch` callouts, same 68-key field, same model
number 518BT.

So there **are** two revisions, and [C-07](#corrections) was wrong to say the
"revised to USB-C" claim was false — it was right, and the mini-USB drawing is
simply the older sheet. What C-07 got right stands: **the outline did not
change across the revision**, which is the part the geometry depends on. The
Type-C sheet could not be sourced at full resolution; the analysis below uses
the mini-USB sheet, whose body silhouette is the same rendering.

Nothing in the model moves. The 34 × 8 mm service window on the left flank
clears either connector.

**The corner is not a constant radius.** A sub-pixel trace of the rear view
gives a circle-fit radius that depends on how much of the corner is included:

| span | circle R | rms |
|---|---|---|
| ±5 mm | 5.87 | 0.034 |
| ±11 mm | 7.30 | 0.164 |

A true arc does not do that. The four corners agree with **each other** to
0.08 mm, so the moulding is uniform corner to corner — what it is not is
circular. A symmetric superellipse fits the two uncorrupted corners at
n ≈ 1.74, but that sits *below* 2, meaning more cut away than an arc, which is
also exactly what a lit render's shading would produce at 45°.

**So the honest limit: this is a marketing render, not an orthographic
projection.** Its silhouette carries the edge roll and its own shading, and no
amount of curve fitting separates moulding shape from rendering artefact. The
dimension callouts are authoritative; the outline is not.

The band therefore stays set by the two **authored** CAD sources — a Shapr3D
STEP with `CIRCLE` entities of exactly 6.5, and the replica's exact tangency at
7.000 — and the design does not depend on resolving it further: the retaining
lip holds a full 1.00 mm for any real corner from 4.0 to 7.0, 0.98 at 7.3, and
degrades only past 8.0.

### C-12 to C-19 — the measured-hardware pass, and a full re-derivation

The owner put calipers on a real board, and a 24-agent re-derivation went back
to Waveshare's own DXF, STEP and drawing, the FCC exhibits and the reference
meshes: **212 findings, 50 disputed, 14 upheld** after adversarial refutation.

**C-12 · The board screws were getting a counterbore, not a countersink.**
The screws supplied with the board have a sloped head; the back plate was
cutting a flat-bottomed 4.6 mm recess. A countersunk head in a counterbore
lands on the shoulder edge instead of on a cone: it does not seat, it sits
proud, and it wedges the bore. Now ISO 10642, 5.0 × 1.50. The stock screw is
4.90 mm overall, which through a 3.20 mm plate leaves **1.70 mm biting the
standoff — 0.68 × diameter** where 1 × is the usual minimum, so the BOM now
specifies M2.5 × 8 countersunk instead.

**C-13 · Shell fasteners M3 → M2.** On the owner's instruction, and the better
fit for the space: the flank strip is 8.35 mm and an M3 boss at 7.4 nearly
filled it where an M2 boss at 6.6 leaves room. Every `m3_*` name was renamed
`shell_screw_*` rather than left holding M2 values under an M3 name. The trade
is recorded: four M2 screws close a 110 g shell easily but are a weaker
accessory anchor, so DESIGN.md no longer advertises them as rigging points.

**C-14 · The bottom tongue-and-groove did not hold — blocking.**
Both the groove and the tongue are `cube(..., center = true)`, which centres in
**Z** as well as X and Y. `tongue_z` was written as if it were the groove's
base, so the groove sat at z 0.000–1.600 — open to the chassis's outer face,
with no lip beneath it. The tongue was not captured in Z at all and the plate's
bottom edge could simply lift away. Separately `tongue_depth = 3.0` left
**0.20 mm** of bottom wall outboard of the groove, half an extrusion.

Now `tongue_z = back_t/2` (groove 0.800–2.400, 0.8 mm of chassis above and
below) and `tongue_depth = 1.6` (1.6 mm of wall, four extrusions, 1.2 mm of
engagement). Two new checks assert the tongue has chassis material **above and
below** it and that the wall survives; both fail on the old geometry.

**C-15 · The two service windows were not mirrored.** Both sat the same
distance from the spine-side edge, so a keyboard turned end-for-end met solid
wall, and the deck was asymmetric for no reason. The second is now the first
reflected about the bay centreline.

**C-16 · `display_aper_draft` 1.45 → 1.50.** `measure_reference.py` sectioned
0.05 mm below the bezel's outer face. On a 45° draft that inset shrinks the
opening by exactly 0.05 per side, so a 1.50 flare read as 1.45. The tool was
sectioning inside the very feature it was measuring.

**C-17 · The "physically excluded" argument is withdrawn.** C-07 claimed a
109.22 mm body could not enter the reference's 109.200 mm pocket. It does not
follow — 0.02 mm is inside injection tolerance and a pocket is not a gauge. The
unit-conversion argument stands without it.

**C-18 · The battery bay is disputed, and the calipers win.** The STEP says the
holder body is 21.10 along V; the owner measured a real board and confirmed
22.10. Both are recorded, because they may be measuring different things (body
versus footprint including the skirt) and because 22.10 is conservative in
**both** roles it plays — it makes the clearance cut larger and the component
mock larger.

**C-19 · Two values kept, their justifications deleted.** `kbd_keycap_tol` was
justified by a replica that is a featureless envelope, not a measurement of a
keyboard. `kbd_access_w/h` were tagged `[MEASURED]` when they are a chosen
envelope *containing* the reference notch, not a reading of it — retagged
`[DESIGN]`.

**And one the audit got wrong**, recorded because it nearly moved a datum: that
the reference tray's R6.100 sets a hard *upper* bound of 6.1 mm on the
keyboard's corner. It sets a **lower** bound. A rounder body has *more* corner
clearance, not less — its corner retreats further from the box corner than the
pocket's does. Brute-forced to 4.66 mm before anything was changed.

### C-11 — The keyboard corner radius was an artefact of the fitting window

[C-08](#c-08--a-guessed-corner-radius-hid-a-defect-that-a-1-d-check-could-not-see)
replaced a guessed 5.0 mm corner with a "measured" 10.0 mm, band 9.5–11.2, from
two sources. **Both were the same methodological error, and the error was mine.**

A least-squares circle fitted over a window that also contains the straight
edges is no longer fitting an arc, and it inflates with the window size. The
same corner on the replica STL reads:

| window | radius | rms |
|---|---|---|
| ±4 mm | 7.00 | 0.003 |
| ±8 mm | 6.99 | 0.004 |
| ±15 mm | 8.78 | 0.227 |

and on the manufacturer's drawing, 5.87 (rms 0.034) at ±5 mm against 12.46
(rms 0.812) at ±20. I used ±14 to ±16 and reported the result to two decimal
places. **The rms column is the tell, and I was printing it without reading
it** — a fit whose residual grows forty-fold is not measuring the thing you
named.

Re-measured arc-only, four sources converge:

| Source | Corner radius |
|---|---|
| Manufacturer drawing, rear view, arc only | 5.87 – 5.96 |
| Third-party CAD replica STL, arc only | 7.000 (tangency 7.000 / 7.000, exact) |
| A Shapr3D STEP carrying authored `CIRCLE` entities | 6.5 exactly |
| Reference ATA tray R6.100 requires a body of | ≥ 4.66 |

Now **6.5 nominal, band 5.9 – 7.0**. The aperture corner derives from it, so it
moved 10.2 → 6.0, which holds the full 1.00 mm lip across the whole corrected
band **and recovers 58.4 mm² of opening**.

One claim in the audit that produced this correction was itself wrong and is
worth recording beside it: that the reference tray's R6.100 sets a *hard upper
bound* of 6.1 mm on the keyboard's corner. It does the opposite. A rounder body
has **more** corner clearance, not less — its corner retreats further from the
box corner than the pocket's does — so the tray sets a **lower** bound, measured
at 4.66 mm. Verified by brute force before the datum was changed.

### C-10 — Every side button and both microphones were sealed inside the wall

The chassis had **no opening at all** for the three side buttons or the two
microphones, and the control dish removed no material. Sixty-four checks passed.

Two independent orientation faults:

- **`rbox()` extrudes from z = 0 to +t, not centred on z = 0.** After
  `rotate([90,0,0])` that runs *inward* from the translate point, so starting
  the cutter at `top_wall_y - wall/2` reached the inner face at y = 66.35 and
  stopped 1.60 mm short of the outer face at 69.55. Five blind pockets on the
  inside of a solid wall.
- **The dish was outside the part.** `rotate([90,0,0])` maps local +Z to global
  −Y, so an aperture built narrow-at-z=0 widens as it goes *inward* — backwards
  for a dish cut from outside. `mirror([0,0,1])` was used to correct that and
  instead placed the entire cutter at y > `top_wall_y`, clear of the wall,
  removing nothing. It is now `rotate([-90,0,0])` with the narrow end at the
  dish floor.

Ray casting proves it: before the fix, 181 rays fired inward at button height
returned a first hit at y = 69.5500 at **every** x — the top face was dead flat.

**Why nothing caught it.** Every one of the 64 checks measured a dimension.
Not one asked whether a hole was a hole. A new `OPENING` class now fires a ray
at each stated aperture and asserts it crosses **no** surface — and asserts the
wall between the buttons still crosses two, so the test cannot be satisfied by
deleting the wall. Verified against the original geometry: it reports six
failures.

Its first version was wrong twice over, both worth stating: it probed the side
ports at y = 0 when the board bay sits at y = 31.3, reporting two perfectly good
tunnels as sealed; and it sampled the dish only across ±15 mm when the dish
spans ±15.9, so every sample sat on the dish floor and max − min was zero
however deep it was.

### C-09 — Two defects the dimensional checks could not see

Both were found by eye, in a render, after being committed and published — which
is the part worth recording, because this repository's whole argument is that
numerical gating beats inspection.

**The apertures were nearly square-cornered.** `rse_aperture()` called

```
rse_plate(w + 2*flare, h + 2*flare, cr + flare, n, q)
```

into a module declared `(w, h, t, cr, n, q = 16)`. The thickness argument was
missing, so every argument after the second shifted left: `cr+flare` landed in
`t`, `n` landed in `cr`, `q` landed in `n`, and `q` fell back to its default.
The top plate of the loft was extruded **10.8 mm tall with a 2.0 mm corner at
exponent 16** — very nearly square.

The apertures still opened to the correct width and height, so the envelope
checks, the clearance checks, the lip check and the whole reference audit
passed. What it got wrong was the corner: **10.2 mm and 4.2 mm collapsed to
about 1.3 mm by the visible face**, and the cutter was 13.219 mm tall for a
2.42 mm cut.

OpenSCAD cannot warn about this. Omitting a positional argument is legal.

An argument-arity checker was written first and **does not catch it** — the call
passes five positional arguments into five required parameters, so it is
arity-legal; the error is a wrong value in the right slot. That checker was
deleted rather than kept as reassurance. What replaced it is
`tools/test_primitives.py`, which renders each primitive on its own and measures
what it actually produced. Its `rse_aperture` case asserts the cut is exactly as
tall as asked and that the corner **grows** with the flare instead of collapsing.

Its first version then produced a *spurious* failure — `rbox` reading 0.116 mm
under nominal — because the test did not inherit `$fn = 64` from
`parameters.scad` and so measured OpenSCAD's default resolution. The test was
wrong, not the model. It now sets the resolution explicitly and states the
faceting budget (0.0096 mm across at `$fn = 64`) rather than hiding it in a
loose tolerance.

**The acrylic window was an orphan.** `window.stl` was exported as a part,
listed in the BOM and shipped, and it fits nowhere. Its outline is the
*reference's* `plexiglass.dxf`, and the reference's board pocket is 13.0 mm —
board 10.75 + acrylic 2.0 + 0.25 clearance. This design's pocket is 11.0 mm:
board 10.75 plus a 0.25 squeeze on a foam gasket. **Dropping the acrylic is
where 2 mm of this deck's thinness came from**, and the part was simply never
deleted with it. It was also 0.72 mm larger than this pocket in both axes, so it
could not have been fitted even flat.

Removed as a part. The outline stays in `parameters.scad` as provenance — it is
a good measurement of somebody else's component — with an assert that now states
the contradiction out loud instead of letting a future edit re-adopt it. The
display needs no window: it sits 2.65 mm below the outer face behind a 2.4 mm
panel.

**Both checks that should have caught these were one-dimensional.** The panel
check compared `display_aper_w >= display_active_w` — widths and heights, which
only ever measure the flats. The active area of an LCD is square-cornered and
the aperture is not, so the reveal is narrowest at the corners: **0.298 mm
there against 1.00 on the flats**, with the corner bounded above at about 5.0.
That is now measured around the whole ring from the rendered mesh, exactly as
the keyboard lip already was after [C-08](#c-08--a-guessed-corner-radius-hid-a-defect-that-a-1-d-check-could-not-see).

### C-08 — A guessed corner radius hid a defect that a 1-D check could not see

`mock_keyboard()` carried `body_r = 5.0` tagged `[PROVISIONAL]` — a guess, never
measured, and the only description this project had of the keyboard's corners.

The real radius is about **10 mm**. Two independent sources agree:

| Source | Method | Result |
|---|---|---|
| Riitek product drawing, rear view | circle fit to the silhouette, scaled on the printed 108.5 mm | 10.8 – 11.2 mm |
| Third-party CAD replica STL | circle fit by section height | 9.5 – 10.6 mm |

Neither is a dimensioned callout, so it is `[MEASURED]` with a band rather than
`[VENDOR]`. **The band matters in both directions, and they are not the same
direction for every check** — a squarer body is the worst case for getting into
the pocket, a rounder one is the worst case for the lip holding it. Anything
checking a corner has to say which end it is using.

**What the guess was hiding.** At 5.0 mm the keyboard's corner stayed well
inside the aperture and every check passed with a healthy 1.00 mm lip. At the
real 10 mm the corner retreats far enough that the superelliptical aperture
corner — which bulges *toward* the box corner — no longer covered it. The lip
went **negative: −0.84 mm at nominal, −1.34 mm at the top of the band.** Four
open gaps into the pocket, and no retention at any corner.

**Why nothing caught it.** The lip check compared `kbd_aper_w < kbd_pocket_w`
and the same in height. That is a one-dimensional test of a two-dimensional
problem: widths and heights only ever measure the flats, and the lip fails at
the corners. It is replaced by one that walks the whole aperture ring, taken
from the rendered mesh, against the body at the worst end of the corner band.

**A second defect surfaced while measuring it.** Both component pockets were cut
`+ 1` proud instead of `+ 0.01` — the only two epsilons in the file that were not
0.01. That is not an epsilon, it is a millimetre taken off the thickness of the
retaining lip, leaving 1.4 mm of a 2.4 mm panel, and it put the bearing plane
inside the aperture's draft flare where the opening has already widened. Fixed
to 0.01. It also moved the structure: the weakest section improved from 294 to
332 mm³ and mean bending stiffness from 1.97× to 2.07× the reference, because
the material came back exactly at the weakest station.

The lesson is the one this file keeps relearning, in a new costume: a
`[PROVISIONAL]` value that gates a check does not fail loudly. It passes,
against itself.

### C-07 — The "retail body" at 109.22 mm was this project's own round trip

For one day this file carried two rival keyboard bodies: the drawing/manual
figure 108.5 × 58.2 × 10.2, and a "current retail" body at
109.22 × 58.42 × 10.16 taken from riitek.com's `4.3 × 2.3 × 0.4 in`. The fit
mocks were built from the **larger of the two**, on the reasoning that a
correction must never loosen a safety margin.

The reasoning was right. The second body was not real.

The manufacturer's own product drawing prints both units on every axis in a
single string — `108.5mm/4.3inch` — which fixes the direction of the
conversion. 4.3 in is 109.22 mm, so the millimetre figure cannot come from the
inch figure; the inch figure comes from the millimetre one. **109.22 was this
project converting 108.5 to 0.1-inch granularity and back, then treating the
result as evidence.** It is also physically excluded: the reference ATA tray is
a built, working device with a 109.200 mm pocket, and a 109.22 mm body does not
go into it.

Two further claims fell with it. The drawing is the *current* product page and
labels a **mini-USB** charging port, so "revised to USB-C" was false. And the
2011 manual and the current drawing agree to the digit, so whatever explains the
mass discrepancy, it is not a change of outline.

Nothing in the geometry moved: the pocket was stated, not derived, and it clears
the corrected body by more than it cleared the phantom. What changed is that a
fabricated datum is gone, and the worst case is now an *assumed tolerance*,
tagged as an assumption, rather than a number dressed as a vendor figure.

This is the third correction to this one datum — [C-06](#c-06--the-ata-tray-is-not-a-press-fit-and-the-002-mm-agreement-was-luck)
withdrew a press fit, O-01 withdrew a rounding band — and the pattern is worth
naming: **every one came from treating a derived or rounded restatement as an
independent source.** Two numbers agreeing is not corroboration until you know
which of them came first.

### C-06 — The ATA tray is not a press fit, and the 0.02 mm agreement was luck

For most of this project's life D-04 argued that the reference ATA tray's
109.200 mm was *"4.3 in to within 0.02 mm, i.e. a deliberate zero-clearance
press fit"*, and leaned on that agreement as strong corroboration of the
vendor's figure — it was described here as "the single strongest datum in this
report".

With the true body now known to be **108.5 mm**, that tray is a **+0.70 mm
clearance fit** and the 0.02 mm agreement was coincidence between two rounded
numbers: 4.3 in converted to mm happens to land near a pocket that was sized
with ordinary clearance over a different figure.

Nothing in the geometry changes — the pocket was already generous enough — but
the *reasoning* was wrong, and it was wrong in the most seductive way: a
suspiciously exact agreement that felt like evidence. Recorded because the
lesson generalises. An agreement to two decimal places between a rounded figure
and a measured one is not corroboration; it is two numbers that happen to be
close.

### C-05 — Corner radii that bite

Twice, a generously rounded pocket corner left material exactly where a
component's much sharper corner needed to be:

- the board pocket's R3.0 corners fouled the PCB's R0.50 corners by 0.33 mm;
- the battery cowl cavity's R8 corners fouled the holder's R2.0 corners by
  1.39 mm.

Both radii are now explicit parameters, bounded and asserted. The general rule:
with `c` mm of per-side clearance around a component of corner radius `r`, a
pocket corner radius much above `r + c/(√2 − 1)` will interfere.

---

## Open items

Gaps that remain. Each is stated with what it would take to close it, and with
how the design is shaped so the gap cannot cause a clash.

### Measured once, not re-audited

Every keyboard-facing dimension in this file is re-derived from the reference
meshes by `tools/audit_reference.py` on each run — **except the service
window** (`kbd_access_*`). The reference tray is open to the exterior along the
same short edge that carries the notch, so the notch cannot be separated
reliably from the surrounding opening; an extraction that looked like it worked
returned the 37–43 mm open edge rather than the 34 mm window.

It is recorded here as measured-once rather than counted among the audited rows,
because a datum that silently stops being checked is how the other corrections
in this file happened.

It gates nothing: the manufacturer's drawing confirms the charge port and the
power switch share one short edge, and the 34 × 8 mm window on the **left**
flank clears either connector type — the owner's Type-C unit and the mini-USB
one on the drawing alike. (This design cut a window on both flanks until
[C-22](#corrections); the keys only read one way up, so the second window
reached nothing and the mirrored pair put the useful one off the features.)

### O-01 — Keyboard outline — CLOSED. Its tolerance is not.

The outline is settled by two independent manufacturer documents twelve years
apart; see [D-04](#d-04--keyboard-outline). **108.5 × 58.2 × 10.2 mm.**

What remains open is narrower. Neither document states a **moulding tolerance**,
and neither says whether the 10.2 mm thickness is measured to the moulding's top
face or to the keycap crowns. A third-party CAD replica of this keyboard
measures 10.600 mm overall, which is where the assumed +0.40 mm band comes from.

The 75 g / 64.8 g mass discrepancy between the 2011 sample and current retail is
real but does not touch the outline. The charge port **does** differ between
revisions — the owner's unit is Type-C, the drawing on file is mini-USB — see
[C-20](#corrections). It drives no geometry: the service window is 34 × 8 mm on
the left flank and clears either connector.

*Mitigation*: the pocket clears an assumed ±0.30 mm in plane and +0.40 mm on
thickness, and the 34 × 8 mm service window clears either connector type, so
the port revision does not drive geometry.
*To close*: calipers. **Thickness first** — it is the only axis with no slack
left against its assertion.

### O-02 — Keyboard charging-port connector type

The FCC-certified body (2011) is micro-USB. One review claims current production
is USB-C. Riitek says only "USB Charging Cable".

*Mitigation*: irrelevant to this design. Both reference enclosures, and this
one, cut a 34 × 8 mm access window rather than a close-fitting port hole, so the
connector type does not drive geometry.

### O-03 — Which switch is PWR, which is BOOT, which is KEY

The STEP designators are KEY4 (U 36.25), KEY3 (U 46.25), KEY1 (U 56.25), but the
function-to-designator mapping is not stated in the STEP, the drawing or the
wiki text.

*Mitigation*: all three apertures are identical and the button sprue is
symmetric, so the enclosure is indifferent. Only the label in
[ASSEMBLY.md](ASSEMBLY.md) is affected.
*To close*: read the official schematic PDF.

### O-04 — Edge-feature heights vs the reference — RESOLVED

*Recorded because it was an open item for most of this design's life, and
because the resolution is the useful part.*

Waveshare places the button centres at W = −0.70 and the microphones at
W = −0.50, i.e. 4.45 mm and 4.25 mm below the display glass front. Measuring the
same apertures in `stl/ata/Caseback.stl` and referencing them to that design's
bezel underside gives 6.9 mm and 6.55 mm — a consistent ≈2.4 mm offset on both
features, which ruled out a one-off error but left the cause unknown.

**Cause found.** The reference's board pocket is **13.000 mm deep** while the
board's actual stack — display glass front to standoff seating plane — is
**10.75 mm**. Its pocket carries about 2.25 mm of slack, and its apertures are
cut for a board resting on the pocket *floor*. This design locates the board
against the *front lip* instead, so the two are measuring from opposite ends of
a stack with slack in it. The offset is 2.25 mm; the discrepancy was ≈2.4 mm.

A second measurement confirms the reference also discards Waveshare's stand
base: its pocket is 71.1163 × 94.5193 against a bare PCB of 69.1098 × 92.5098,
which is **1.0032 / 1.0047 mm per side — symmetric**. Against the 70.10 mm stand
base the clearance would be an implausibly lopsided 1.01 / 0.508.

*Resolution*: the factory position is used, referenced to the display glass
front, which is the plane this enclosure locates against. The apertures are
5.4 × 4.4 mm around a 4.553 × 2.203 mm switch body, absorbing about ±1.1 mm
either way regardless.

### O-07 — Board mounting-hole diameter, two readings

Two independent passes over Waveshare's CAD package disagree: the STEP `BOARD`
solid yields Ø4.20 through-holes (24 CIRCLE instances at radius 2.1000), while
the DXF front view reads as a Ø2.10 hole inside a Ø4.70 pad.

*Mitigation*: it does not matter here. This enclosure puts nothing in those
holes — the M2.5 screws thread into the SMTSO-M2.5-7ET standoffs, and the back
plate's own clearance is Ø2.70. Both readings are consistent with M2.5.

### O-05 — PCB outline tolerance

The drawing gives explicit tolerances only for the TFT (±0.10) and the active
area (±0.10). `92.5 PCB OD` and `69.1 PCB OD` carry none. Ordinary PCB routing
tolerance is about ±0.13 to ±0.2 mm.

*Mitigation*: the pocket carries 0.50 mm per side, comfortably more than routing
tolerance.

### O-06 — Keyboard corner radius

Modelled as R5.0 `[PROVISIONAL]` for the fit-check mock only. Inferred as ≈6.6
from the ATA pocket's base fillet, but that fillet is the ATA designer's choice
and the proof-of-concept has none, so the two references disagree.

*Mitigation*: the pocket corner radius is 6.0 and the pocket is 0.49 mm per side
larger than the keyboard, so a smaller real radius only adds clearance.

---

### O-08 — The button sprue did not fit behind the wall — CLOSED

Measured inward from the chassis's top outer face, on the rendered parts:

| Plane | Distance in | Space behind the wall |
|---|---|---|
| outer face | 0.00 | |
| control-dish floor | 0.90 | |
| top wall, inner face | 3.20 | 0.00 |
| PCB top edge (pocket clearance 0.50/side) | 3.70 | **0.50** |
| switch actuator face (0.19 inside the PCB edge) | 3.89 | **0.69** |

A flange behind the wall has to live in that 0.50 mm, and something has to
reach 0.69 mm to press the switch. **Both cannot be satisfied at once**, and
the sprue failed it from both directions before it was fixed:

- **Too long.** The original was 6.59 mm overall — cap 3.80, flange 1.20, post
  1.60 — needing 3.39 mm behind the wall. Seated with its flange on the wall
  the flange ran 0.70 mm into the PCB's edge and the post a further 1.60 mm
  through it; seated with its post on the switch, all three caps stood 2.70 mm
  proud and held PWR, BOOT and KEY permanently pressed.
- **Too short.** Cut back to cap + a 0.40 mm flange it fitted, with its deepest
  feature 0.35 mm behind the wall — and **0.34 mm short of the actuator**. The
  caps rattled and never reached the switches.

The 0.40 mm flange is measured from the reference enclosure, whose board pocket
carries **1.00 mm per side**. This one carries 0.50. The retention scheme did
not come across with the number.

**Resolved by moving the flange inside the wall.** A 1.00 mm counterbore behind
the apertures — one continuous slot, so the sprue's connecting webs recess with
the flanges — takes the flange, so at rest nothing protrudes past the wall's
inner face and the whole 0.50 mm is left for the plunger. The flange is 0.40
thick, so the counterbore also supplies **0.60 mm of free travel**, bought from
the wall's own thickness instead of from the board's clearance. The plunger is
offset in Y to −0.20 on the button axis, spanning −1.00 to +0.60 inside the
switch body's ±1.10 band, so it lands on the switch and misses the PCB's edge
entirely.

**And then the depth was still wrong, for a third reason.** 0.690 mm is where
the actuator is if the board is exactly where the drawing says. It is not: the
board is located by four M2.5 screws in ISO 273 close-fit 2.7 mm holes, so it
floats ±0.10 mm and the actuator is anywhere in **0.590 to 0.790**. A plunger
cut to 0.690 would hold a switch permanently pressed on any build that floated
toward the wall. The plunger is therefore cut to **0.540** — the near end of
the band, less a 0.05 mm margin — so the gap at rest is 0.05 to 0.25 mm and is
never zero, and the 0.60 mm of travel crosses the worst gap and still delivers
the switch's 0.25 mm throw with 0.10 mm to spare.

That last error was found by a different instrument than the ones that found
the first two: putting the sprue where the assembly puts it and intersecting it
with the chassis as a solid. The depth arithmetic was self-consistent and still
wrong, because it had no opinion about the board's mounting float. `validate.py`
now runs that boolean at rest, mid-travel and fully pressed.

**Why neither version was caught for so long.** `buttons` is a separate part,
exported laid flat for printing, and it was never placed in assembly space by
a fit check — only its bounding box was measured, and a bounding box was never
going to say whether 6.59 mm of anything can exist in 3.89 mm of space. The
`STACK` class now measures the sprue against the two planes above.

### O-09 — The keyboard lip goes negative at a corner — CLOSED

`_corner_lip()` measured the front-face lip with the keyboard **centred**.
Nothing centred it. With the body at its low tolerance (108.20 × 57.90) pushed
hard into a corner of what was then a 110.20 × 59.40 pocket — ±1.00 in X and
±0.75 in Y — the narrowest lip was **−0.361 mm** at that corner against
**+0.985 mm** centred. You would have seen a sliver into the pocket past one
corner. The keyboard was never at risk of escaping: every edge and the other
three corners held ≥ 1 mm against a 106.5 × 55.8 aperture.

Closed by taking the play out rather than by moving the aperture: the pocket is
now 109.85 × 59.15 with locating ribs, and the same worst case measures
**+0.368 mm**. `tools/validate.py` asserts it from the rendered chassis over
the body's whole tolerance band *and* every position the pocket allows.

This was trap 5 from the project's own list — *a part's bounding box in
isolation is not where the assembly puts it* — applied to the header
(`expansion_body_h`, C-21) and not to the keyboard.

---

## Measure these before a final print

The design is asserted consistent, not proven against hardware. Nobody has held
these two parts against a printed chassis. Before committing filament to a final
build, put calipers on:

1. **Keyboard THICKNESS** — O-01. The outline is settled, but 11.0 mm of pocket
   sits exactly on its assertion against a 10.6 mm upper band, and the drawing
   does not say whether its 10.2 mm includes the keycaps.
2. **PCB outline and the standoff seating plane** — confirms D-02 and D-03 and
   the decision to discard the stand base.
3. **18650 holder protrusion past the standoff plane** — sets the cowl rise.
4. **Button and microphone heights below the display glass front** — O-04 is
   resolved on paper but rests on a chain of three inferences; it is cheap to
   confirm with the board in hand.

`tools/validate.py` proves internal consistency. It cannot prove that the datums
match reality; only calipers can do that.

### C-41 — The carry case: three rejections, one plane

Version 1 of the sleeve passed every check it had. The verdict named three
things none of those checks asked about — *"those lugs sit in a way that make
them super fucking fragile and awkward from a geometric standpoint, also this
should echo the form of the device more directly. also there is no method of
inserting those magnets whatsoever, no one could get their little grabbers in
there to do that."*

All three were true, and the third is the one that mattered, because it was not
a styling complaint. It was a defect.

### The magnets could not be fitted, and could not have held anything anyway

The pockets opened into a cavity 155 mm deep, closed on five sides. Nothing
reaches that. No check had asked whether a feature could be *assembled*, only
whether it was geometrically correct, and it was geometrically correct.

Worse, checking the retention arithmetic that had never been done:

| gap to the deck's disc | 2.00 mm — its own 0.80 skin, 0.80 flock, 0.40 clearance |
|---|---|
| inverse square off the 0.80 mm vendor figure | 0.62 N a pair, **2.46 N** for four |
| two-point fit through contact and 0.80 mm | 2.08 N a pair, **8.32 N** for four |
| deck weight | **≈ 3.4 N** |
| what resists, the deck leaving along Y | shear at 20.6 % → 0.51–1.71 N, plus µ≈0.4 friction → 1.0–3.3 N |

Read as favourably as the data allows, four magnets are *comparable to* the
deck's weight, not a multiple of it. They are a **seat**, not a latch, and
parameters.scad now says so where someone would otherwise assume otherwise.

### Splitting it on a plane answered all three

The case is now two halves joined by eight M5 × 25 socket screws into hex nuts
trapped at the parting face — driven from the front with one key, because no
socket reaches down a 16 mm flank. The split was chosen for access, and paid
four more times:

- both halves print **face-down and flat**: measured **0 mm² of near-flat
  ceiling** in each, against a budget of 20
- the magnet pockets open **upward on the bed** and are filled by hand
- the inside is two open trays, which is the only sane way to flock it
- the back no longer needs a spine to stand on

### The spine was a support trap, and the fix cost 11 mm of depth

The one-piece back carried a raised spine for the cowl channel. Printed
back-down, the spine crown is the first layer and the slab bottom sits
**11.00 mm above it** — a downward-facing flat face **20 mm wide over the full
155 mm, 3,100 mm² a side**. Flaring the spine out to meet the slab does not
rescue it: 11 mm of rise over 28 mm of run is **21°**, half of what FDM holds.

So the back drops to the channel floor everywhere. It costs 11 mm of depth and
returns a part with nothing under it — and a solid rectangular block is the
more honest object.

### Form: it was square, and it was square because of the fastener

The first attempt at this revision put the fasteners in the flank, which an M5
nut needs **15 mm** of. That made the case **150.65 × 155.45 — square**, where
the deck is plainly portrait at 1.2065. It had lost the proportion in service of
a nut, which is the wrong thing to lose it for, and no check asked.

So the flank went back to 8 mm and the fasteners moved into the rails, which
have 22 mm of material anyway. Three numbers are now pinned to the deck and none
to taste:

| corner | `corner_blend × case_w / body_w` | **12.97** |
|---|---|---|
| mouth height | solved so `case_h/case_w == body_h/body_w` | **15.00** |
| exponent | `form_n`, unchanged | **3.2** |

Offsetting the deck's corner outward by the wall would have given 20.40 mm on a
135 mm body — proportionally almost twice as round as the deck, which is why v1
read as a pebble. `check_case.py` now measures the ratio: **1.2065 against
1.2065**. The flat plinth v1 needed to stand on the bed is gone with the print
orientation that forced it, so top and bottom are the same corner.

### Lugs: a rail, not a tab, not a hole in a wall

v1 cut a 4 mm slot through a 10 mm flank *at the top corner*, where the outline
is already turning — 3 mm of wall each side. v2, written in this same
revision, replaced it with a 32 mm pad on each flank. That measured strong and
it read as **two tabs stuck to a box** — the same bolted-on look that got the
grip fingers thrown out in C-38, arrived at again by a different route.

A tab is a local answer to a global problem, which is the lesson C-39 already
recorded and which did not transfer. So the third version is not local: **one
squared band per flank, 14 mm proud, 134 mm long**, carrying all four fasteners
*and* the strap slot.

| | v1 | v2 (tab) | now (rail) |
|---|---|---|---|
| material each side of the slot | 3.00 mm | 7.50 mm | **6.50 mm** |
| depth behind it | 27.25 mm | 38.25 mm | **38.25 mm** |
| shear section a side | 82 mm² | 287 mm² | **249 mm²** |
| length of flank it structures | 16 mm | 32 mm | **134 mm** |

The rail gives up 38 mm² of shear against the tab and buys four times the
length of engaged flank, which is the trade worth making. Both ends stop inside
the **straight run** of the flank, so a termination is always a clean step and
never a step onto a curve. The slot sits 47 mm below the mouth: lugs at the rim
foul the hand drawing the deck out, and a bag hung from its rim tips forward.

### Two checks in this file were worth less than nothing

`check_case.py` gained a seam test, and the first two versions of it **passed on
anything**:

1. It measured containment against `trimesh.util.concatenate([front, back])`.
   The halves share a face at the joint, so a ray crossing two coincident
   surfaces flips parity twice and `contains()` reports solid material as open
   air. It failed three true checks — *false* failures, which is the cheap
   direction. Fixed with a real boolean union.
2. It compared the mating faces by summing `polygon.exterior.area`. Shapely's
   `.exterior` is a **LinearRing**, and a ring has zero area. The check read
   *"outlines 0 and 0 mm², 0.00 % apart"* and passed. It would have passed on
   any two shapes in existence.

Fixing (2) to real areas was still not enough: narrowing the section by 0.6 mm
moves its **area** by 0.4 %, under any sane tolerance. The joint is now compared
as **rings, in millimetres** — `hausdorff_distance` — which reads 0.001 mm on
the true pair and 0.330 mm on the deliberately mismatched one.

**Three instruments, two of them worthless, before one measured the thing.**
The pattern this file keeps recording is not that geometry is hard. It is that
a check computing the wrong quantity is more dangerous than no check, because
it is reported as a pass.

### The two readers of parameters.scad did not agree

Deriving the mouth height put `case_rim` above the `case_w` it depends on.
`tools/params.py` resolved the forward reference and reported **15.00 mm**.
OpenSCAD left it **undef** and propagated undef through every dimension
downstream. Every Python gate in this repo passed on a parameter set the
renderer could not evaluate.

Two asserts happened to touch the affected values and caught it. That was luck:
moving `case_edge_ch` the same way is silent — no assert touches it, the part
still renders, and it renders **without its chamfers**.

`validate.py` now echoes **every scalar parameters.scad assigns** out of
OpenSCAD itself and compares it against what params.py believes — 382 of them,
checked for undef and for drift. Verified to fail on exactly that silent case
and to pass on the corrected file. Two checks, 116 → 118.

The lesson is narrower than "tools disagree". It is that **the forgiving reader
is the one every gate runs on**, so the gates were all measuring a file the
renderer never saw.

### C-42 — The rails clashed with the curve, and the fasteners only went down the sides

Two complaints, and they turned out to be one fault: *"the combination of the
rectangular shapes where the holes are, plus the squircle-esque shape come
together at this weird angle the geometry clashes. Based on the curves and the
rectangular, the screw holes need to also attach all the way around not just on
the sides."*

A rail is a **straight bar** laid against an outline that is straight in the
middle and curved at the ends. Its ends always land somewhere the body is
turning, and the wedge between them reads as a mistake. And a rail can only
exist where the body is straight — which is exactly why the fasteners could
only be on the sides. Same fault, two symptoms.

### The fasteners are the outline now

There is no list of screw coordinates anywhere in this project. `ring_path()`
takes the case's own outline, insets it to the middle of the wall, and samples
it at even arc length:

    inset outline  ->  arc length  ->  13 fasteners at a 35.7 mm pitch

So they follow the superellipse **round the bottom corners** instead of
stopping where a straight bar would have to. Measured on the rendered part: 12
gaps between **32.1 and 35.8 mm**, spread 10.3 % — and the low end is geometry,
not error, because a chord under-reads an arc. Nothing can drift off the form,
because the ring *is* the form.

### The ring is a U, and that is physics, not a concession

A fastener parallel to Z needs material through the **whole depth**. Across the
mouth there is none — the deck's own cross-section has to pass through there.
The flanks and the floor have full-depth metal; the mouth cannot. So the ring
runs as far up both flanks as it can and stops, and `check_case.py` asserts it
**turns the corners**: 5 fasteners below the deck, 2 of them out past the cavity
in both bottom corners.

### It was square, because of a nut — again

A 16 mm wall is what an M5 nut needs (9.47 mm across corners leaves 3.27 mm of
metal either side, and the ring runs down the middle of it). At 16 mm all round
the case is **150.65 wide**, and holding the deck's proportion at that width
makes it 181.75 tall. C-41 solved the same tension by shrinking the flank; that
option is gone once the fasteners have to go round.

Holding the proportion fixes the case's **height**. It does not say where to
spend it, and that is the actual decision:

| | mouth | floor | consequence |
|---|---|---|---|
| spend it at the mouth | 24.3 mm | 16.0 mm | deck sits down a hole, needs a scallop to reach |
| **spend it at the floor** | **12.0 mm** | **28.3 mm** | invisible, no scallop, 28 mm of PLA on the drop end |

### The scallop that got built and thrown away

The 24 mm mouth was built, with an **80 × 22.3 mm r47 arc** cut through both
halves to reach the deck. It worked. It was also, on a 150 mm face, not a
detail but *the silhouette* — it turned a brutalist slab into a tote bag.
Shrinking it to a subtle 8 mm dish keeps the silhouette and stops solving the
problem: you cannot reach 24 mm down through an 8 mm relief.

Moving the height into the floor removes the problem instead of styling around
it. Recorded so nobody adds the scallop back without first asking why the mouth
is 12 mm.

### Five strap lugs, and the one that ruled out a family

| version | what it was | why it went |
|---|---|---|
| 1 | 4 mm slot through a 10 mm flank, at the corner | thin web, awkward place |
| 2 | 32 mm pad on the flank | read as a tab stuck on |
| 3 | 134 mm rectangular rail | **clashed with the curve** — this correction |
| 4 | tangent stadium, 8 mm proud | still read as an ear |
| 5 | superellipse pad, 46 mm, form_n 3.2 | — |

Version 4 failed for a reason worth writing down, because it rules out a whole
family of answers. **Tangency between two parallel faces 8 mm apart can only be
made by a semicircle of radius 4** — no larger radius is tangent to both — so a
tangent boss always ends in a tight 4 mm turn, and a tight turn at each end is
what an ear looks like. The escape is a long shallow swell, and that is
geometrically unavailable here: the slot has to sit high on the flank for a bag
to hang flat, a swell centred there runs out of straight flank within about
44 mm, and a 44 mm swell needs r34 ends — a **40° junction, worse than the
stadium it replaced.**

So the boss stays local and stops fighting the outline. It **speaks it**: a pad
on the deck's own superelliptical corners and the deck's own exponent. The
complaint was that a rectangle and a squircle met at a weird angle. There is no
rectangle now.

### A boss that measured, rendered and photographed while not existing

Replacing the stadium with the pad was done with two `str.replace()` calls. The
first deleted the old module along with its comment; the second, which was
supposed to rewrite that module, therefore matched nothing and **silently did
nothing**. OpenSCAD does not stop for this — it prints

    WARNING: Ignoring unknown module 'lug_pad'

and renders the part without it. The render was produced, looked at, and
described as *"integrated rather than hung on"* — of a boss that was not there.

`build.sh` has treated that warning as fatal for the enclosure for a long time.
The render that fooled me was an ad-hoc `openscad | grep '^ERROR'` that did not.
`check_case.py`'s own `render()` now treats it as fatal too, so running the file
directly is no weaker than running the gate.

The lesson is not "read the warnings". It is that **a guard only guards the path
it is on**, and the convenient path around it is the one that gets used while
iterating.

### What caught what

Of the defects in this correction, the checks caught the pad (two failures, both
real) only because `check_case.py` had been rewritten to find the fastener bores
**in a section of the actual part** rather than read their coordinates from
parameters. The headline number it reports — `166.6 over the strap bosses`
against a 150.65 body — is the one that said the boss was missing.

Two checks in the same file had to be fixed before they were worth anything:

1. The port-burial check probed a point 13 mm into the wall. The strap slot
   passes through the outer half of the wall **directly outboard of the microSD
   port**, so the probe landed in fresh air and called a port with 7.5 mm of
   metal over it exposed. "Buried" is a thickness, not a yes/no; it is measured
   with a ray cast now — USB-C 24.0 mm, microSD 24.0 mm, keyboard 16.0 mm.
2. The ring-spacing check walked the fasteners nearest-neighbour from bottom
   dead centre. The ring is a **U, not a loop**, so that walk runs out to one
   end and then jumps 134 mm across the open mouth to pick up the other side —
   reported as a **236 % spacing error** on a part that is evenly spaced. It
   starts at an end now.

### C-43 — Thirteen screws that clamped nothing

An adversarial review of the C-42 case, run across five independent lenses,
confirmed four findings out of twenty-three claims. Two lenses — print and
structure — arrived separately at the same one, and it is the worst defect this
project has recorded:

**The thirteen M5 screws put zero clamp force across the joint.**

### Why

The hex pockets opened at the parting face. A screw pulls its nut **toward the
head**, and on that side the pocket had no roof — so the nut rose the 0.20 mm
of float and bore on the **front half's own parting face**. Head and nut then
both reacted against the front half. The load closed on itself inside one part.

Measured on the rendered halves, probing the nut's bearing annulus (r = 3.2 mm,
outside the Ø5.40 bore, inside the hex's 4.10 mm inradius) at all 13 sites and
18 angles, just below the joint:

| | |
|---|---|
| back-half material above the nut | **0 / 234** |
| front-half material the nut bears on | **234 / 234** |

`parameters.scad` had encoded the fault in its own arithmetic and nobody read
it: `case_bolt_stack = (case_z1 - case_split_z) + case_nut_h` — front half plus
nut pocket, with **zero back-half thickness in the stack**. The assert then
checked a 25 mm screw against it and passed.

So **8,300 mm² of mating face carried nothing**, and the two halves were held
together by four slip-fit Ø4 pins.

### All twenty checks passed, and two of them certified it

- *"every nut pocket is enclosed in material"* probed a **lateral** ring and
  never looked up.
- *"every screw bore runs front face to nut"* asserted the axis was **clear** —
  it actively certified the absence of the material that would have clamped.

This is the project's named defect class in its purest form yet: the geometry
that mattered was geometry no check interrogated, and the checks that existed
were confidently measuring the wrong thing.

### The fix

The hex is now a **counterbore at the back face** with **10.93 mm** of back-half
metal above it. The nut bears **up** on that roof, pushing the back half onto
the front half, and the bore runs all the way through:

    head -> front half (19.125) -> back half (10.925) -> nut (4.70)
    stack 34.75 mm, screw M5 x 35, tip 3.25 mm inside the back face

It still assembles with one hex key and no spanner: the hex keys the nut against
rotation, and a nut dropped in loose is caught by the screw and drawn onto its
seat. The back face gains thirteen hex wells — the "unbroken back" of C-41 is
gone, and that is the right trade for a joint that actually closes.

**The check that would have caught it** measures the load path itself: back-half
material in the nut's bearing annulus, from its seat to the joint, at every
site. Verified to fail on the C-42 geometry — **468/936** — and pass on this one
at 936/936.

### The nut was the wrong nut

`case_nut_t = 4.00` was labelled **ISO 4032**. 4.00 is the **DIN 934** figure;
ISO 4032 M5 is m = 4.40 min / **4.70 max**. A legal ISO nut would have stood up
to 0.50 mm proud of a pocket cut for it, and the joint would have closed only by
ploughing all thirteen nuts into their pocket floors. Now 4.70, which accepts
either standard.

The `case_fit = 0.20` comment also claimed a "press fit" while specifying
**+0.10 mm a side of clearance**. It is a clearance fit; the comment says so now,
and explains why that is correct here — the hex only has to key the nut against
rotation, because the screw seats it.

### Nine [DERIVED] comments were lying

The review's minor finding was two stale `[DERIVED] = N` comments. Checking the
whole file found **nine**, seven of them in the frozen enclosure and stale since
whatever edit moved their inputs:

| | claimed | actual |
|---|---|---|
| `front_face_half_h` | 68.244 | **68.944** |
| `magnet_boss_d` | 8.50 | **8.70** |
| `magnet_y_lo` / `magnet_y_hi` | 7.975 / 54.575 | **8.575 / 53.600** |
| `cover_mouth_w` / `cover_mouth_h` | 114.902 / 138.902 | **114.502 / 138.502** |
| `case_y_floor` / `case_cy` | −87.325 / 3.550 | **−99.627 / −8.751** |
| `case_nut_h` | 4.200 | **4.900** |

**No geometry moved** — every expression was right; only the numbers a reader
would trust were not. `validate.py` now checks all 52 such claims against the
value they name, matched strictly on the file's own `[DERIVED] = N` form so that
prose containing an equals sign is not mistaken for a claim. 118 → 119 checks.

### What this says about review

The C-42 work ran twenty checks, four gates and a visual inspection, and shipped
a case that does not bolt shut. What found it was **five reviewers who had not
written it**, told to refute rather than agree, with instructions to measure the
mesh rather than read the source. Nineteen of their twenty-three claims did not
survive their own verification pass — the four that did were worth the other
nineteen.

### C-44 — Take the ornament off

*"Thats an absurd amount of M5 bolts, and these bolts should go all the way
through industrial interesting brutalist, the form should be more natural and
flowing and smoothed ... output the fundamental fundamental ass shrink wrapped
shape but robust, two part, elegant, and I will work on creating the silouette
more intersting in tinkercad."*

Four things, and the last one changes what the job is: this is now a **base
object for someone else to shape**, so everything that was there to be looked at
comes off and only what has to be right stays.

### Thirteen to seven, and why not six

Thirteen at a 35.7 mm pitch was instrument-case spacing applied without asking
whether this is an instrument case. Seven: bottom dead centre, both bottom
corners, both mid-flanks, both flank **tops**.

Six was tried first — sampled on half pitches so nothing sits at dead centre,
which is tidier. It is the worse object. It puts the topmost fastener **44 mm
below the mouth** and leaves the one end of the ring that is already open
unclamped. Seven costs one bolt and holds the mouth shut. Measured: 6 gaps,
66.1–70.7 mm, 6.6 % spread.

### The bolt goes all the way through

Head proud on the front face, plain hex nut proud on the back, nothing recessed.
It is what was asked for and it is also the only one of the three arrangements
tried here that is structurally obvious — C-43 had to reason carefully about
where a buried nut bears; a through-bolt has nowhere for the load to
short-circuit. **M5 × 45**, ending 2.05 mm past the nut's far face.

The cost is a spanner. Nothing keys the nut, because a hex recess deep enough to
hold it needs 7.73 mm of metal outboard and the rolled edge does not leave it.
Seven nuts, one 8 mm spanner.

### Rolled, not chamfered

A chamfer is two arrises and a flat — it reads machined. `rse_soft` lofts the
outline through a smoothstep whose value **and first derivative** both vanish at
the face, so the surface arrives there with zero slope and leaves no arris at
all.

It is also, unexpectedly, the more printable edge:

| | chamfered (C-43) | rolled |
|---|---|---|
| near-flat ceiling | 0 mm² | **0 mm²** |
| face under 44° | 206 mm² | **0 mm²** |

The 206 mm² was the 45° chamfers themselves sitting exactly on the limit. A
roll whose derivative vanishes at both ends is **vertical where it meets each
face** and only reaches ~28° in the middle, so there is nothing marginal left.

`case_soft` is not free, though: the bores are straight while the surface rolls
inward, so every millimetre of roll is a millimetre off the metal outboard of a
bore. That is what moves the ring off the wall's centreline —
`case_bolt_ins = (case_side + case_soft) / 2`, which puts 3.80 mm each side
instead of 8.00 inboard and 5.00 out.

### Six strap bosses, and then none

| version | what it was | why it went |
|---|---|---|
| 1 | slot through a 10 mm flank, at the corner | thin web, awkward place |
| 2 | 32 mm pad | read as a tab stuck on |
| 3 | 134 mm rectangular rail | clashed with the curve (C-42) |
| 4 | tangent stadium | still read as an ear |
| 5 | superellipse pad | the best of them, and still an object stuck on |
| 6 | **nothing** | — |

The wall is 16 mm because an M5 bore needs it to be. That is already enough to
put a slot straight through with **4.00 mm of metal either side and 38.25 mm of
depth** — 153 mm² in shear a side, far past anything a strap applies. **The boss
was never carrying the load. It was carrying the idea of carrying the load.**

### Shrink-wrapped is not available, and here is the number

"Shrink wrapped" cannot mean thin walls while M5 bolts pass through them:

| thread | bore | min wall | case width |
|---|---|---|---|
| M5 | 5.40 | 14.4 | 147.5 |
| M4 | 4.50 | 13.5 | 145.7 |
| M3 | 3.40 | 12.4 | 143.5 |

Dropping two thread sizes buys **4 mm** of width on a 150 mm object. The cavity
alone is 118.65 wide. So the wall stays at 16, and what "stripped back" actually
buys is the ornament: no bosses, no chamfers, no counterbores, six fewer bolts,
and an unbroken silhouette to work from.

### The guard held this time

Rewriting this file broke halfway through a scripted edit and left
`carrycase.scad` referencing three variables that no longer existed. The render
guard added in C-42 — `WARNING: Ignoring` treated as fatal — caught it on the
first render, named all three, and cost about a minute.

C-42 records the same class of failure costing an entire review cycle and a
render I looked at and described approvingly. The difference between the two is
one `grep`.

### C-45 — The widest line was the seam

*"the corner radius for the smoothing shouldnt be individual for each side so
that they come together with a crease in the middle, it should feel like a
seamless single object"*

C-44 rolled **each half separately, from the seam outward**. Both halves were
therefore at their widest AT the parting plane and the surface curved away from
it in both directions — so the object's widest line ran all the way round at
mid-height. Two pillows stacked, not one case.

The outer form is built once now, over the whole 38.25 mm, and the halves are
cut out of it. The roll belongs to the **object**, and lives at its two outer
faces where an edge actually is. Measured through the depth:

| z | −16 | −8 | −4 → +10 | +16 | +20 |
|---|---|---|---|---|---|
| width | 144.68 | 149.45 | **150.65** | 147.89 | 145.17 |

Straight for 14 mm through the middle, which is where the seam falls. The joint
chamfer drops 0.60 → **0.30**: a hairline, not a shadow gap, because the object
is meant to read as one piece.

It is built as the **intersection of two one-ended rolls facing opposite ways**.
Each is full width where the other is rolled, so the intersection takes the roll
at both faces and full width between. They cross only where both are at full
width *and* both have zero slope, so they meet tangentially and add no line of
their own.

### 0.01 mm over 8,800 mm²

The first build of it failed `the halves do not interpenetrate` by **86.87 mm³**
— which over the 8,792 mm² mating face is exactly **0.01 mm**. `rse_plate`
extrudes upward from its origin, so the mirrored half's pinch plate sat one
plate-thickness past the parting plane and the two halves overlapped across
their whole joint.

Harmless in print and wrong in the model, and the only reason it was seen at all
is that the check measures a boolean intersection volume rather than asking
whether the two halves *look* like they meet.

### Open, and waiting on reference images

Three of the same message's asks are not resolved and are deliberately not
guessed at:

1. **M5 × 20 does not fit.** The depth is set by the deck (16.85) plus its
   battery cowl (11.00) plus flock and walls: **38.25 mm**, none of it styling.
   A 20 mm screw entering the front face reaches z = +2.05 and stops 18.25 mm
   short of the back face where the nut goes. M5 × 40 is the shortest that
   reaches an inlaid nut.
2. **Inlaid hex on the back** needs 7.73 mm of metal outboard of the bolt axis
   and the rolled edge leaves 1.77 mm at the face. It needs either a thicker
   wall, a smaller roll, or the ring moved inboard against its cavity margin.
3. **The silhouette and the strap lugs.** Six lug versions have now been
   rejected (C-38 → C-44) and each was inferred from a verbal description. The
   owner offered reference images; that is a better instrument than a seventh
   guess, and this is recorded as an open item rather than another attempt.

### C-46 — Heat-set inserts, an off-centre seam, and a captive D-ring

*"instead of the bolt going all the way through it should be 7 total bolts and
we use M5x10 mm heat inserts on one side ... the holes for the lugs should not
be rectangles they should be holes and they should allow for a D ring ... the
sillouette can be rectangular but not be just a brick, the gemoetry can be more
intersting and midcentury modern."*

### The insert changes three things at once

| | through-bolt | heat-set insert |
|---|---|---|
| what the wall carries | M5 nut, 9.47 across corners | **Ø7.00 insert** |
| wall it needs | 15.47 | **13.00** |
| what the screw spans | the whole 38.25 mm object | **one half** |
| screw | M5 × 45 | **M5 × 20** |

So **M5 × 20 works after all** — it was impossible as a through-bolt and is
comfortable here, because the screw only has to cross the front half. The wall
drops 16 → 13 and the case narrows 150.65 → **144.65**.

The C-43 load path still has to be right, and an insert gets it right for a
different reason than a through-bolt does: it is anchored in the back half's
plastic by its knurls, so tension runs head → front half → insert → back half
with nowhere to short-circuit. Measured: 84/84 probes solid round every bore,
grip **8.95 mm = 1.79 diameters**.

### The seam was at exactly 50 %

That is the single most brick-making number in the object, and it was free to
move the whole time. The only constraints are that the cowl channel stays in the
back half and the magnet pockets stay in the front, leaving the window
**z ∈ (−1.20, +18.05)**.

At **z = +11.00** the halves are 11.05 and 27.20 — a **1:2.46** datum line at a
proportion someone chose. It also happens to be what makes the screw work:
11.05 + 8 mm of thread is 19.05.

### Soft in plan, crisp at the face

The previous version softened every axis at once — superellipse corners *and* a
3 mm roll at both faces. An object with no defined planes reads as a pillow. One
axis gets the softness now: generous corners in plan, a hard **1 mm chamfer** at
the faces, so there is a top plane and a bottom plane and all the turning
happens at the corner.

### The D-ring is trapped, not bolted on

A closed ring cannot be threaded onto a finished part — but a case that comes
apart can do what a solid one cannot. A **Ø5.20 bore runs front-to-back through
the flank**, straddling the parting plane; the ring's straight bar lies in it and
its arch comes out through a tapered relief at each end. Close the case and it is
captive. No fixings, no plate, nothing that can work loose, and the mechanism is
invisible.

It is captive because the bore is **closed for 16.45 mm between the two
reliefs** — a 31.75 mm bar cannot lift out through two windows that far apart.
That closed run is the whole retention claim, so `check_case.py` measures it.

**Which ring, and why it matters.** The only axis long enough to take the bar
without running vertically is front-to-back, and that is the case's depth:

| | bar | margin in 38.25 mm |
|---|---|---|
| 1¼ in | 31.75 | **+6.50** — drawn |
| 1½ in | 38.10 | +0.15 — does not fit |

A 1½ in ring needs the case about 4 mm deeper, which is 4 mm of dead air in
front of the deck. One parameter either way.

### The plinth was built and taken out

A stepped foot is a real midcentury move and it cannot coexist with a fastener
ring that goes all the way round:

    the ring crosses the floor 6.50 mm in from the bottom edge, so a bore there
    has 3.80 mm of metal to it. case_bolt_keep wants 3.00. The plinth gets 0.80.

Worse, a plinth **shorter than the corner radius (13.94) sits inside the bottom
corner's curve and never reads as one** — so the version that would read has to
be ~18 mm tall, which puts the two bottom-corner fasteners inside it as well. A
15 mm wall buys 1.80 mm of plinth; that is the trade if it is wanted.

Two print findings are worth keeping from the attempt:

1. Insetting the **depth** as well — the more correct plinth — cannot be
   printed. The halves lie on their faces, so a Z inset is a ledge pointing at
   the bed: **377 mm² of it, measured.**
2. **Tapering that ledge made it worse, not better.** 2.5 mm of rise over 3.3 mm
   of run is 53° off vertical — past the limit rather than under it. I had the
   angle the wrong way round and the measurement caught it. X and Y are both
   in-plane, so an X-only splay would have been free at any angle.

### Two checks that were measuring nothing useful

- The fastener census classified holes **by area**, and the D-ring bore is Ø5.20
  against a bolt's Ø5.40 — 7 % apart, so any tolerance loose enough to find the
  bolts swallowed the D-ring too. Classified by **position** now.
- The plinth check measured **vertices** in a band near the foot. The outline's
  straight flank carries no vertices between its two ends, so it sampled
  whatever happened to be there and reported a **5.52 mm inset on a 2.50 mm
  step**. Sections, not vertices.

Case **144.7 × 174.5 × 38.2 mm**, 459 cm³, ~313 g. 19/19 case checks,
119/119 validate.

### C-47 — Ninety-four per cent of it is shell

*"this thing is gonna eat up filament, this shouldnt be a fucking brick of
plastic ... the fucking attachment of the D ring part should just be a chunky
hole strong robust. not this fiddly little cutout bullshit."*

### The material question, measured before anything was changed

Model volume is not filament. At the repo's own settings — 0.8 mm nozzle,
3 perimeters, 15 % infill — a perimeter shell is **2.4 mm thick**, and this part
is thin-walled enough that almost all of it is shell:

| | model | filament | of which shell |
|---|---|---|---|
| front half | 146.6 cm³ | 146.1 cm³ | **100 %** |
| back half | 312.8 cm³ | 203.0 cm³ | 90 % |
| **total** | 459 cm³ | **349 cm³ → 433 g** | **94 %** |

The front half is *entirely* perimeter: its volume is less than its surface area
× 2.4. **So hollowing saves nothing** — the 15 % infill is only 6 % of the
filament. What drives this part is **surface area**, and surface area is set by
the deck it has to contain.

That reorders every lever:

| | saves |
|---|---|
| perimeters 3 → 2 | **130 g** — slicer setting, no geometry change |
| a 0.6 mm nozzle (3 perims = 1.8 mm) | **98 g** — slicer setting |
| floor 21.06 → 13.00 | 30 g |
| wall 4.00 → 3.60 | 25 g |
| flank 13 → 11 | 5 g |

**The two biggest levers are not geometry at all.** Recorded because four
revisions of this case have been argued about in terms of wall thickness, and
wall thickness is worth 5 g.

### Why the flank cannot get thinner

The chain is short and it closes:

1. The mouth has to pass the deck, so there is **no full-depth material across
   the top** — a fastener parallel to Z cannot go there.
2. So fasteners live in the flanks and the floor.
3. An M5 heat-set insert is Ø7.00 and wants 3 mm of metal a side: **13 mm**.
4. The flanks are the largest single region of the part.

The ways out are an external boss (rejected seven times), M3 instead of M5, or
accepting it. Not a wall-thickness decision.

### What did change

The proportion rule is **gone**. `case_floor` used to be solved so `case_h/case_w`
matched the deck's ratio. That was my idea, not a requirement, and it was buying
a number nobody looks at with **9 mm of solid plastic across a 145 × 38 section**.
The case is now as big as it has to be: **144.7 × 166.4 × 37.4**, 396 cm³,
**390 g — 10 % off**, with the remaining 90 % explained above rather than
hidden.

### The strap lug is a hole

Eight versions now. The last trapped a D-ring's bar in a bore straddling the
parting plane with tapered reliefs for the arch. It was clever and it was wrong:
fiddly to print, fiddly to assemble, and it made the strap depend on two 6 mm
windows.

This is **a hole**. Ø7.00, front to back through the flank, so a cord or split
ring wraps the full 13 mm of wall and hangs outward, and the load goes into the
whole height of the flank above it rather than into any feature. The parting
plane cuts across it, so each half prints it as a plain vertical bore with
nothing overhanging. 3.00 mm of metal either side — the same margin every
fastener bore gets.

Ø7 is what the wall allows. A bigger hole needs a local pad, and a pad is the
thing that has been rejected seven times.

### C-48 — A river rock, and the thin wall that made it heavier

*"thin the walls not around the bolts, and also the bolts need to have a concave
inset so the top of the bolt will lay flush ... the whole exterior ... should be
a seamless smooth river rock, not like a curved rectangle."*

### The form

Two things make it a rock rather than a rounded box, and neither is applied
afterwards:

1. **The section rolls continuously face to face.** `case_roll` at 0.50 means
   the inset is falling the whole way from one face to the middle and rising
   again to the other — no flat band anywhere, no arris.
2. **The wall is 6 mm and swells to 16.5 at each of the nine fastener and strap
   sites**, by pushing the plan *outline* outward with a cos-squared falloff
   rather than by adding a pad. There is no junction to crease at.

Built as **one polyhedron**. A stack of hulls cannot do it: the outline dips
back between swells, so it is not convex and `hull()` would fill the dips.
Swells combine as `1 - prod(1 - f)` rather than summing, so neighbours blend
instead of stacking to twice the amplitude.

### The counterbore, not the bolt, sizes the swells

A flush head needs its Ø9.00 counterbore *plus a rim* to sit **inside the front
face**, and the roll pulls that face in by `case_soft`. That is the whole
constraint chain, and it is what takes the local wall to 16.50.

### Three things measured that reading would not have caught

**The dish is the wide one.** r30 cutting 1.20 deep leaves a footprint
**16.80 mm across** — nearly twice the counterbore it was blending — and it cut
straight out through the rolled edge. A sphere's footprint is
`2·sqrt(2Rd - d²)`, which is not intuition-sized. Now r11 at 1.00: 9.17 across,
1.42 mm of rim. The assert had checked the counterbore and not the dish.

**The roll inset was applied twice.** Once to the base outline and again to the
swell, so the face outline came out at **65.61 where the bolts sit at 65.825** —
four of seven counterbores broke out of the edge.

**The swell was pushed the wrong way.** Radially from the outline's centre, a
point high on a flank is mostly *sideways* from that centre, so only part of a
10.50 mm swell arrives where it is needed: **68.22 measured against 71.83
wanted.** It pushes along the outline **normal** now — for a counter-clockwise
polygon, the outward normal of tangent (tx, ty) is (ty, −tx).

All three were found by sectioning the rendered part and counting closed holes.
A section with **9 closed holes** is a part where nothing broke out; one with 3
is not, and it looks identical in a render until you turn it.

### The thin wall made it heavier

This is the finding worth keeping. C-47 established that **94 % of this part is
perimeter shell**, so surface area is what you pay for. Thinning the wall from
13 to 6 and swelling it back at nine sites:

| | volume | surface | filament |
|---|---|---|---|
| 13 mm wall, flat slab | 396 cm³ | 1310 cm² | **390 g** |
| 6 mm wall + 9 swells | 448 cm³ | 1371 cm² | **430 g** |

**Both went up.** Nine swells at a 26 mm reach overlap, so the wall ends up
thick almost everywhere anyway — the reach is 18 now, which recovers about 12 g
of the 48. And the roll itself adds surface.

So "thin the walls except at the bolts" is a **form** decision, not a material
one. It costs roughly 10 % more filament than the flat slab it replaced, and
that is the honest price of the rock.

### C-49 — The part had a flat face and a 90° arris while the source said it had neither

C-48 shipped with this sentence in `parameters.scad` and again in `CASE.md`:

> *the inset is falling the whole way from one face to the middle and rising
> again to the other, so there is no flat band and no arris.*

The part had **23,665 mm² of dead-flat face** — 88 % of its bounding rectangle —
meeting the flank at a **90.0° edge**, 1,782 edges of it, all the way round both
faces. Twenty checks passed. Every one of them is about holes, metal, clearance
or overhang; **not one looked at the shape.**

It was caught by *looking at the render*, which is the second time in this
project (C-44 was the first) that the renderer was the only thing telling the
truth. The difference is that in C-44 I looked at a render and described a boss
that was not in it; here I looked at a render and saw a claim that was not in
the part. Both say the same thing: **a render is evidence and has to be read
against the claim, not for it.**

### Why the flat stays

Both halves print **face-down**, which is what makes the two-part split pay: one
flat bed face and one open tray each, no bridge, no support. Any surface that
blends smoothly out of a flat bed face leaves a near-horizontal *downward*
band all the way round the rim — the one overhang FDM cannot do unsupported.
Crowning the face outward is the same fault: 3 mm of crown over 75 mm of radius
is a 5° ceiling across the whole face.

So the plateau is not a defect and is **reported, not budgeted**. The arris is
the defect, and it is now a deliberate **4.00 mm facet at 55° off horizontal** —
the same number twice, because that angle is also the overhang angle when the
face is on the bed, and 45° is the limit.

### Three things had to be wrong for a 4 mm facet to render as 0.47 mm

Cutting the facet changed the measured rim from 90° to **83°**. It had 0.473 mm
of run where 2.80 was asked for. Two faults, in the loft:

**The swell was evaluated at the moving outline.** As the inset falls the
outline walks *away* from each site, the cos-squared falloff drops, and the
swell shrinks by roughly what the inset just gave back. Inside a swell the two
cancel and the wall comes out vertical. The C-48 comment already claimed the
swell was "a constant push"; the code did not do that.

**Each level was its own narrowed superellipse.** Narrowing it by `2·ins` also
narrows its corner radius by `ins` — and **moving a corner slides every vertex
along the flank.** Vertex *j* sat at a different *y* on every level, so it
sampled the swell somewhere else each time. Fixed by offsetting **one**
reference outline along its own normals: vertex *j* now stays on one ray for the
whole depth, so the swell is genuinely constant and the inset is genuinely the
inset.

And one fault in the new check itself, which is the part worth keeping:

**It located each edge at the midpoint of its two face centroids.** A cap
triangle can be 60 mm long, so a strap-hole rim reported itself 24 mm from where
it was and walked straight through the "ignore anything near a fastener" filter.
Every hole rim in the part — 90° by definition — was being counted as the
silhouette. It also measured on `front.union(back)`, and the boolean remeshes
the rim into slivers that read as 180° edges. It measures each half on its own
mesh now, at the real edge midpoint.

### What it measures

**55.0° on a straight flank, 60.7° at its worst**, which is on a swell shoulder:
there the outline runs oblique to the push, so 2.80 mm along the normal buys
less than 2.80 mm of true run and the facet comes out steeper. Steeper is the
safe direction for an overhang, so it is allowed for rather than chased. The
check's budget is 63°; an arris is 90°.

### The honest summary

It is **not a river rock**. It is a stone worn flat on two sides. A form with no
flat anywhere needs supports on the outside faces or a split that puts no face
on the bed, and both cost more than the shape is worth. Filament went 430 → 436 g.
