kylebsmith/ESP32-S3-RLCD-cYbErDeCk/docs/img/backplate-rear.png

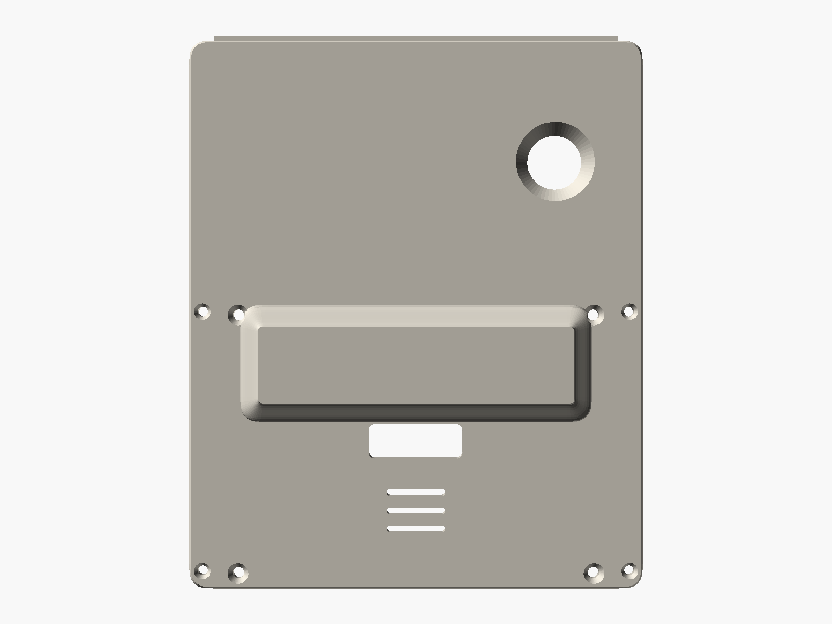
docs/img/backplate-rear.png
