kylebsmith/ESP32-S3-RLCD-cYbErDeCk/docs/img/case-back.png

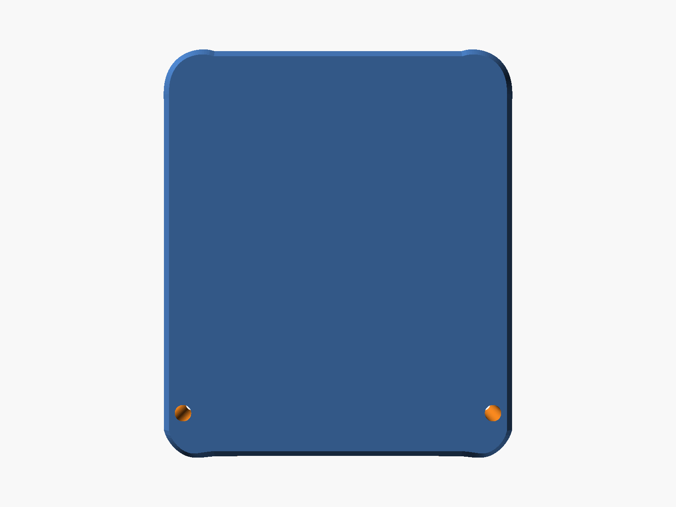
docs/img/case-back.png
