kylebsmith/ESP32-S3-RLCD-cYbErDeCk/docs/img/case-flank.png

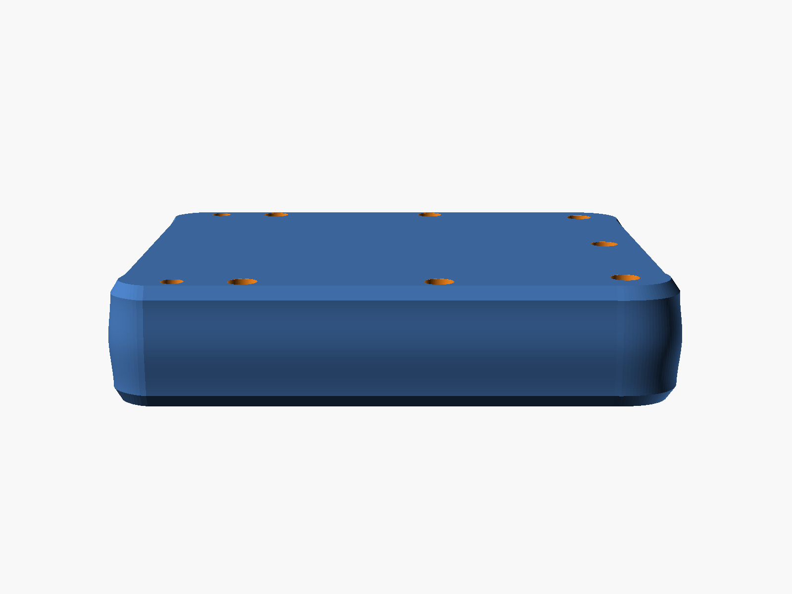
docs/img/case-flank.png
