kylebsmith/ESP32-S3-RLCD-cYbErDeCk/export/drawings/sheet2-backplate.png

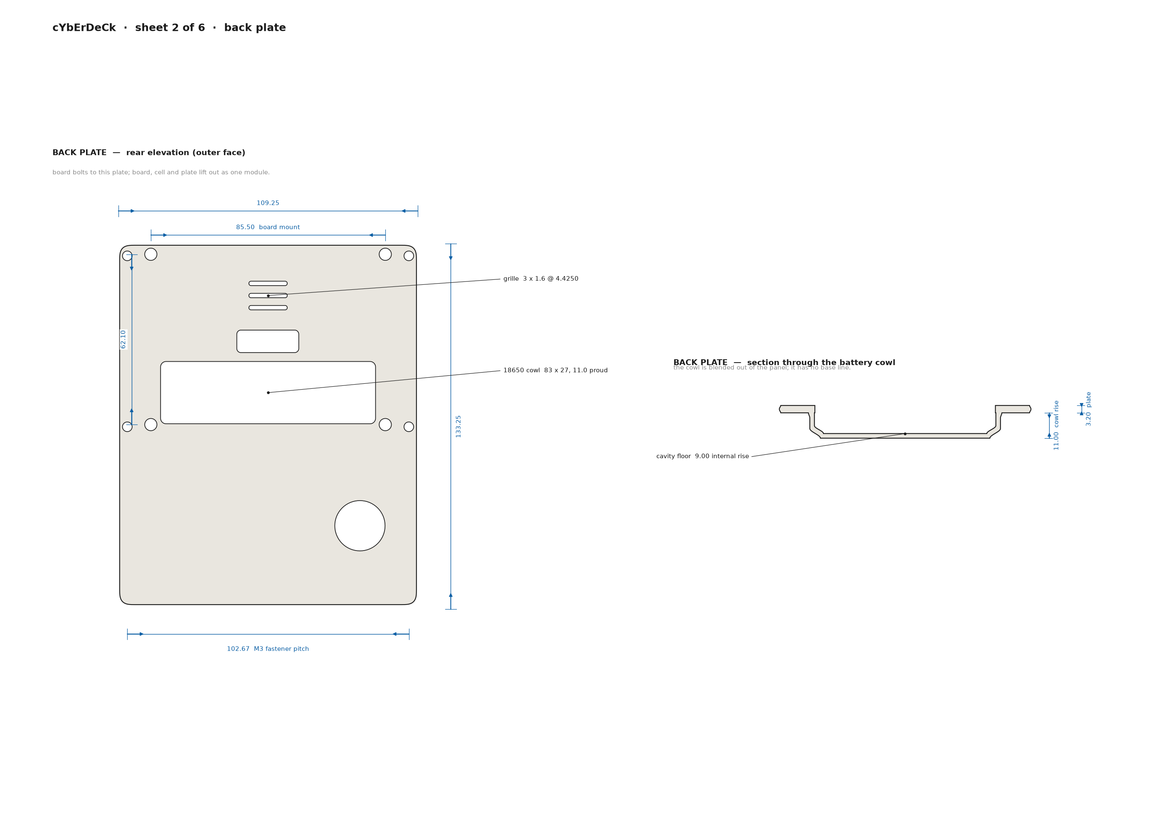
export/drawings/sheet2-backplate.png
