kylebsmith/ESP32-S3-RLCD-cYbErDeCk/export/drawings/sheet5-structure.png

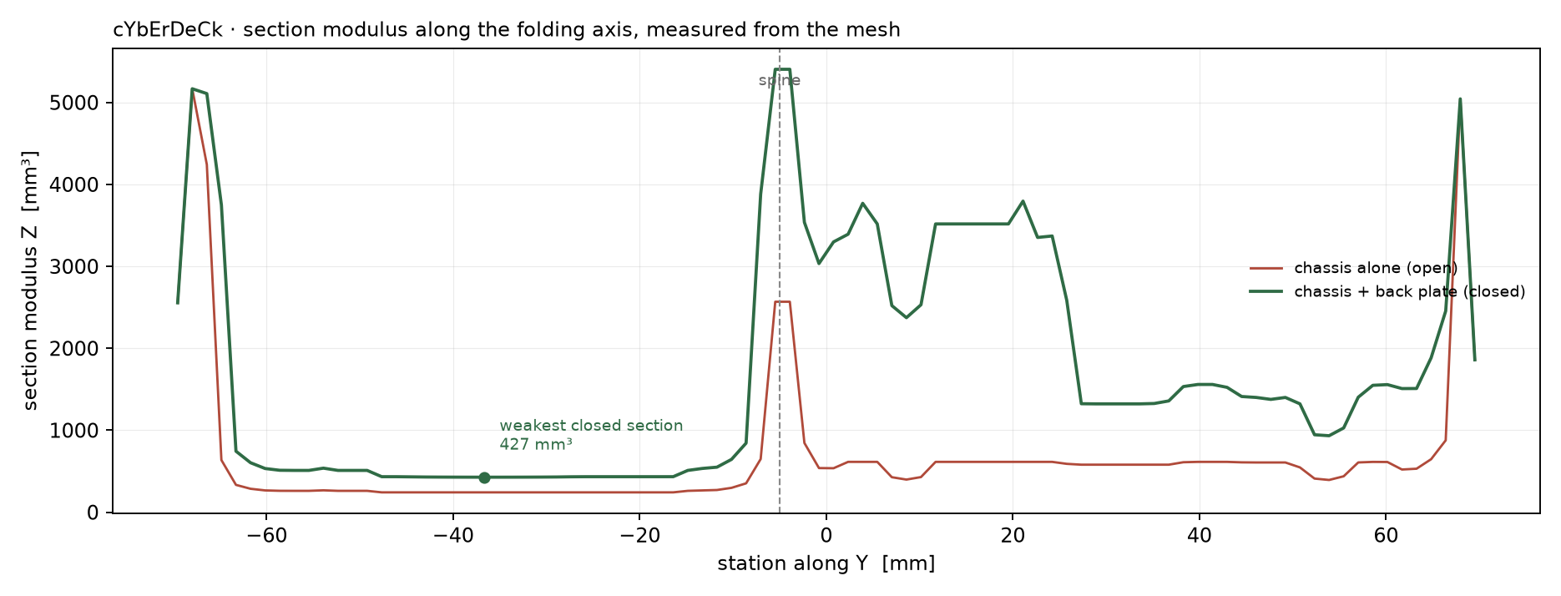
export/drawings/sheet5-structure.png
