kylebsmith/ESP32-S3-RLCD-cYbErDeCk/export/drawings/sheet6-corner-lip.png

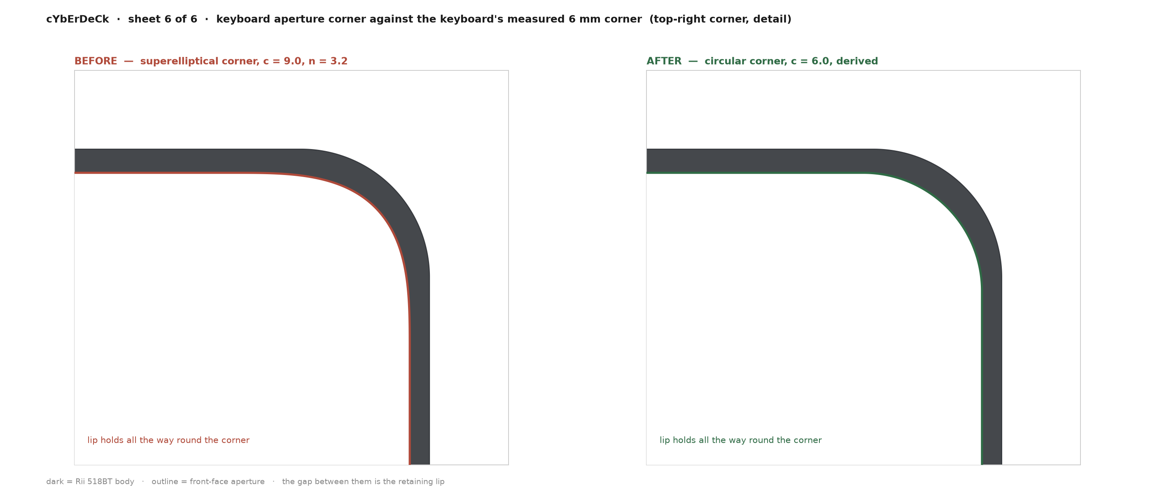
export/drawings/sheet6-corner-lip.png
