kylebsmith/ESP32-S3-RLCD-cYbErDeCk/export/drawings/sheet4-components.png

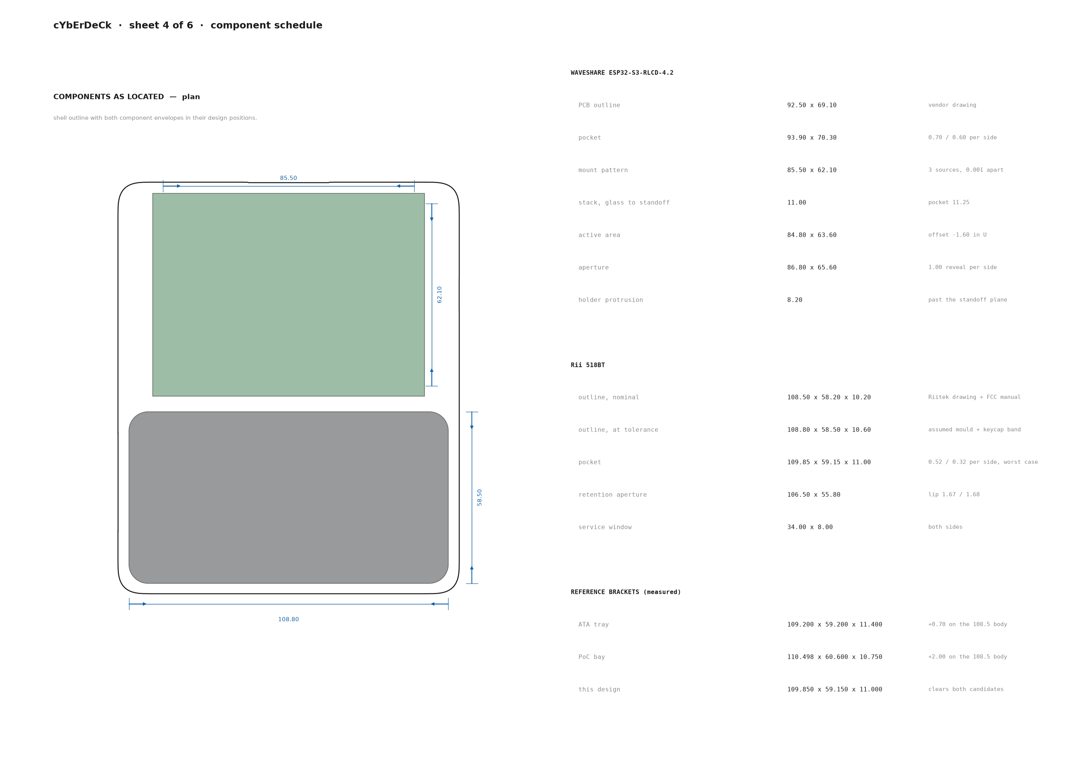
export/drawings/sheet4-components.png
