kylebsmith/ESP32-S3-RLCD-cYbErDeCk/docs/img/render-assembly-front.png

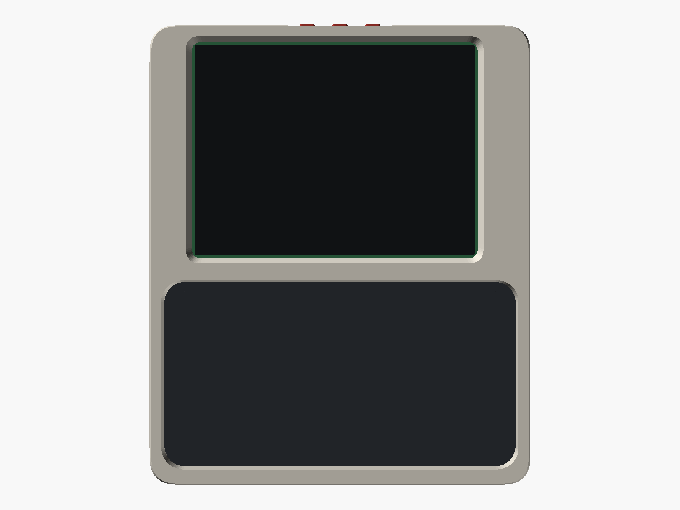
docs/img/render-assembly-front.png
