kylebsmith/ESP32-S3-RLCD-cYbErDeCk/docs/img/render-assembly-iso.png

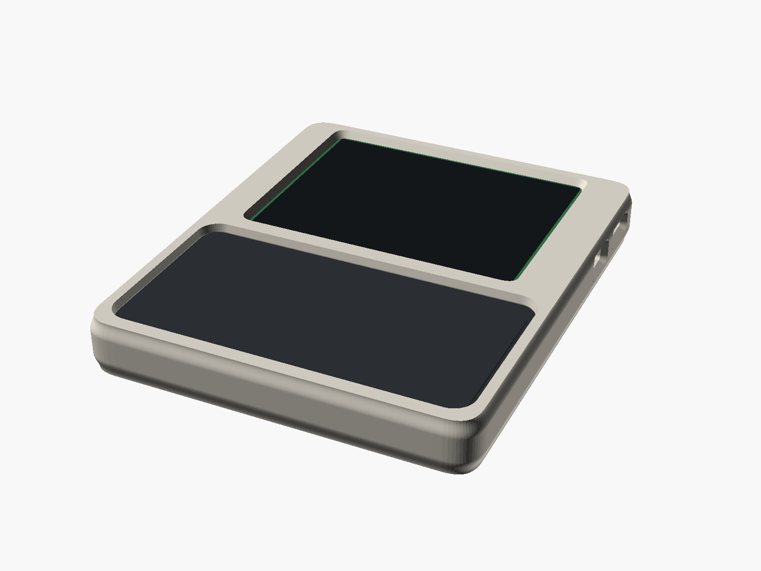
docs/img/render-assembly-iso.png
