kylebsmith/ESP32-S3-RLCD-cYbErDeCk/export/drawings/sheet3-assembly.png

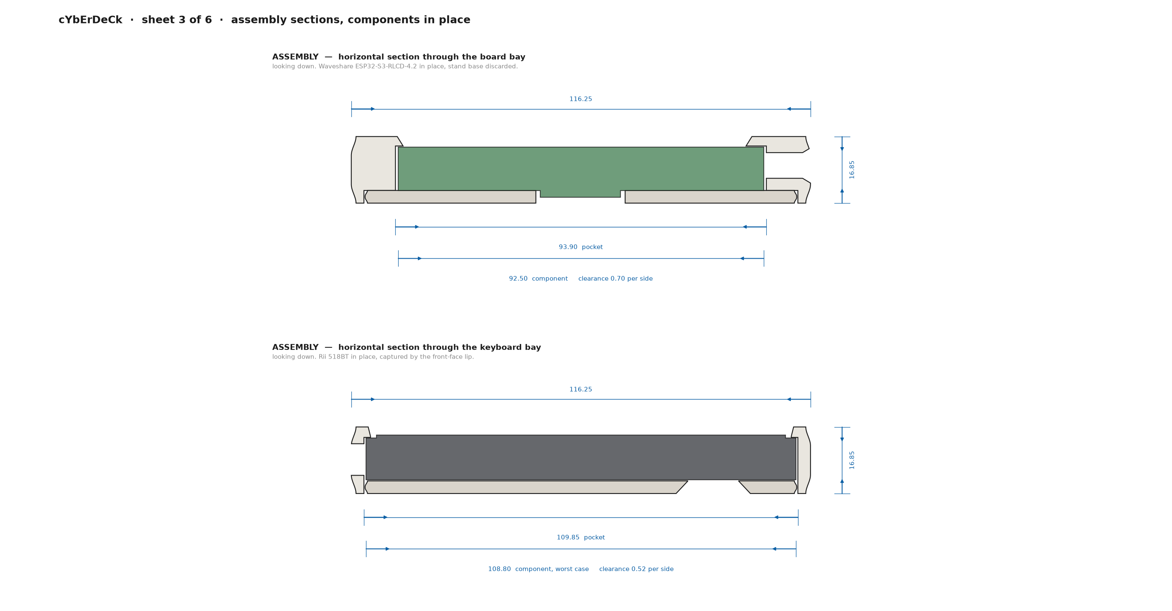
export/drawings/sheet3-assembly.png
