kylebsmith/ESP32-S3-RLCD-cYbErDeCk/firmware/main/editor.c

/*
 * The editor view.
 *
 * LAYOUT, in logical pixels on the 400 x 300 landscape panel. Every vertical
 * figure is a multiple of 12 and every horizontal one is even, because those
 * are the CASET and RASET quanta - a margin that breaks them turns a
 * one-character redraw into a three-character one.
 *
 *     y   0..11    top margin                          12
 *     y  12..251   text, 10 rows of 24                240
 *     y 252..263   gap                                 12
 *     y 264..287   status bar, one row                 24
 *     y 288..299   bottom margin                       12
 *
 *     x   0..19    left margin                         20
 *     x  20..379   text, 30 columns of 12             360
 *     x 380..399   right margin                        20
 *
 * 30 x 10 is 300 characters on screen. Narrower than the 66 x 25 that
 * docs/HARDWARE.md planned for, but that grid was unreadable on the real
 * panel, and margins are most of what makes a page look composed rather than
 * dumped.
 */
#include "editor.h"
#include "battery.h"
#include "cell_attr.h"
#include "viz.h"
#include "ui_text.h"
#include "seq.h"
#include "seq_pattern.h"
#include "lane_name.h"

#include <stdio.h>
#include <string.h>

#include "docstore.h"
#include "cmd.h"
#include "kbd.h"
#include "st7305.h"
#include "esp_log.h"
#include "esp_timer.h"
#include "textgrid.h"
#include "ask.h"

int64_t editor_now_ms(void);
static void line_at(size_t from, char *out, size_t max);
static void cycle_buffer(int dir);

#define MARGIN_X     20
#define MARGIN_TOP   12
#define CELL_W       12
#define CELL_H       24

/* The grid is chosen at runtime, because both faces are already compiled in
 * and the right density is not the same for writing prose and for reading a
 * list of ten commands. Chunky is the default because the panel is
 * reflective with no backlight; dense is there when the screen is the
 * constraint rather than the eyes. */
static int TEXT_COLS  = 30;
static int TEXT_ROWS  = 10;
static int STATUS_ROW = 10;

#define MAX_LINES  2048
/* How far back from the cursor the wrap window starts. The old code wrapped
 * from byte zero, so a document past MAX_LINES display lines stopped growing
 * the table, the cursor line was never found, and the view froze with every
 * further keystroke invisible. Wrapping a bounded window around the cursor
 * removes the cliff and makes the cost independent of document length. */
#define WRAP_BACK  6000

static int  s_line_start[MAX_LINES];
static int  s_line_count;
static int  s_cursor_line;
static int  s_cursor_col;
/* The view is anchored to a document OFFSET, not a line index. wrap() builds
 * its table from a window starting at cursor-WRAP_BACK, so the origin moves
 * as the document grows and every line index shifts underneath it. A line
 * number was a coordinate in a sliding frame; an offset is not. */
static int  s_top_offset;

/* The sticky goal column. Vertical motion CONSUMES it but never overwrites
 * it: goto_line_col clamps to the target line's width and the next wrap()
 * re-derives the column from that clamped position, so without this a single
 * short line passed through en route loses the column for good.
 * -1 means "take it from wherever the cursor is now". */
static int  s_goal_col = -1;

static bool s_cursor_on = true;

/* Where the cursor cell landed at the last draw, so a blink can repaint one
 * cell instead of the frame. */
static int  s_cur_col = -1, s_cur_row = -1;
static char s_cur_ch  = ' ';
/* Whether the playhead is passing through the cursor cell. The blink has to
 * know, or it erases the bar every time it repaints that one cell. */
static bool s_cur_under = false;
static bool s_cur_over  = false;
/* Document offset of the character the last run was refused for, or -1. Set
 * by run_current_line, cleared by the next key that is not pure motion - an
 * edit, a document switch, another run - so it never points at the wrong text. */
static int  s_err_off = -1;
/* When set and in the future, the status bar shows the way out of the output
 * buffer after the command's own message has had its moment. */
static int64_t s_msg2_until = 0;

static char s_status_shown[64];
/* The result of the last command, shown in place of the status line for a
 * few seconds. A command that reports nothing is indistinguishable from one
 * that did not run. */
static char    s_msg[64];
/* Where we came from, so a jump to +out is never a one-way door. An unnamed
 * scratch buffer has no name for >open to match, so without this a command
 * run from fresh writing strands that writing with no key and no command to
 * get back to it. */
static int     s_prev_buf = -1;
static int64_t s_msg_until;
static bool s_chrome_dirty = true;
static uint32_t s_pushes, s_push_bytes, s_render_us, s_cells;
static uint32_t s_cells_total;

void editor_vitals(uint32_t *pushes, uint32_t *bytes,
                   uint32_t *render_us, uint32_t *cells)
{
    *pushes = s_pushes;
    *bytes  = s_push_bytes;
    *render_us = s_render_us;
    *cells = s_cells;
    s_pushes = 0;
    s_push_bytes = 0;
    s_render_us = 0;
    s_cells = 0;
}

uint32_t editor_cells_drawn(void) { return s_cells_total; }

void editor_message(const char *m)
{
    snprintf(s_msg, sizeof s_msg, "%s", m);
    s_msg_until = editor_now_ms() + 6000;
}

void editor_invalidate(void)
{
    s_chrome_dirty = true;
    s_status_shown[0] = '\0';
}

/* TWO DENSITIES, AND THE PANEL DECIDES THAT, NOT TASTE.
 *
 * Cell height must be a multiple of 12 - the CASET addressing quantum in
 * landscape, established in docs/HARDWARE.md and enforced by tg_set_layout -
 * and cell width must be even, the RASET quantum. So the obvious middle sizes
 * are unbuildable here: 9x18 fails on height, 9x24 fails on width ("cell
 * width 9 / origin x 20 must be even"). An 8x24 face was built and thrown
 * away: a 6 px body in a 24 px cell reads 1:4 against the chunky face's 1:2.4,
 * which is thin and barely monospaced, and every body column of the chunky art
 * carries ink so there is no lossless crop - narrowing collapses a 2 px stem,
 * and 2 px stems are why this face is legible on a reflective panel with no
 * backlight.
 *
 *   0  low   12x24   30 columns, 11 rows
 *   2  high   6x12   60 columns, 24 rows
 *
 * Level 1 is not a size. It is left in the numbering so boot documents that
 * name it keep working, and it resolves to high.
 */
esp_err_t editor_set_density(int level)
{
    const tg_font_t *face = (level >= 1) ? &tg_font_6x12 : &tg_font_12x24;
    const int cw = (level >= 1) ? 6 : 12;
    const int ch = (level >= 1) ? 12 : 24;

    const int cols = (ST7305_WIDTH - 2 * MARGIN_X) / cw;
    /* One row of the grid is the status line; the rest is text. */
    const int rows = (ST7305_HEIGHT - MARGIN_TOP) / ch;

    const esp_err_t err = tg_set_layout(face, 1, MARGIN_X, MARGIN_TOP,
                                        cols, rows);
    if (err != ESP_OK) {
        return err;
    }
    TEXT_COLS  = cols;
    TEXT_ROWS  = rows - 1;
    STATUS_ROW = rows - 1;
    s_top_offset = 0;
    s_goal_col = -1;
    editor_invalidate();
    tg_invalidate();
    return ESP_OK;
}

/* A SECRET BEING TYPED (ask.h). While one is open every key goes to it and
 * none reaches the document. */
static ask_t s_ask;
static cmd_secret_fn s_ask_fn;

static bool editor_ask(const char *question, cmd_secret_fn fn)
{
    ask_start(&s_ask, question);
    s_ask_fn = fn;
    editor_invalidate();
    return true;
}

esp_err_t editor_init(void)
{
    cmd_set_asker(editor_ask);
    return editor_set_density(0);
}

/* Greedy word wrap. Records where each display line starts and where the
 * cursor lands. Prose kind: Enter splits and what follows reflows. */
static int s_wrap_origin;       /* document offset the table starts at */

static void wrap(int cols)
{
    const size_t len = doc_len();
    const size_t cur = doc_cursor();

    /* Start a bounded distance before the cursor, then advance to the first
     * character after a newline so the window begins on a real line boundary
     * - wrapping is independent of anything before that point. */
    size_t origin = cur > WRAP_BACK ? cur - WRAP_BACK : 0;
    if (origin > 0) {
        while (origin < cur && doc_at(origin - 1) != '\n') {
            origin++;
        }
    }
    s_wrap_origin = (int)origin;

    s_line_count  = 0;
    s_cursor_line = 0;
    s_cursor_col  = 0;

    size_t i = origin;
    int line_begin = (int)origin;
    int col = 0;
    int last_space = -1;

    s_line_start[s_line_count++] = (int)origin;

    while (i <= len) {
        if (i == cur) {
            s_cursor_line = s_line_count - 1;
            s_cursor_col  = col;
        }
        if (i == len || s_line_count >= MAX_LINES) {
            break;
        }
        const char ch = doc_at(i);

        if (ch == '\n') {
            i++;
            line_begin = (int)i;
            col = 0;
            last_space = -1;
            s_line_start[s_line_count++] = line_begin;
            continue;
        }
        if (ch == ' ') {
            last_space = (int)i;
        }
        col++;
        i++;

        if (col >= cols) {
            int brk = (last_space > line_begin) ? last_space + 1 : (int)i;
            if (brk <= line_begin) {
                brk = (int)i;
            }
            if ((size_t)brk > cur && cur >= (size_t)line_begin) {
                s_cursor_line = s_line_count - 1;
                s_cursor_col  = (int)(cur - line_begin);
            }
            i = (size_t)brk;
            line_begin = brk;
            col = 0;
            last_space = -1;
            s_line_start[s_line_count++] = line_begin;
        }
    }
}

/* The status bar is chrome, not part of the document grid, so it is drawn at
 * its own pixel row and only when its text actually changes. */
static void line_at(size_t from, char *out, size_t max);

/* Messages must fit, and "fit" is checked at BUILD time now, not hoped for.
 *
 * tg_draw_text_px used to clip silently at the screen edge, so "not a command
 * - start the line with >" rendered as "not a command - start the line" and
 * lost the entire point of the sentence. That was "fixed" by moving the clip
 * into the snprintf below - which truncates just as silently, at exactly the
 * same column, and the owner hit it. Fixed messages now live in ui_text.h
 * behind _Static_assert. See the note at the top of that file. */
#define STATUS_MAX TEXT_COLS

static void status_bar(void)
{
    char wide[96];
    char s[STATUS_MAX + 1];

    if (s_ask.active) {
        ask_render(&s_ask, wide, sizeof wide);
    } else if (s_msg[0] != '\0' && editor_now_ms() < s_msg_until) {
        snprintf(wide, sizeof wide, "%s", s_msg);
    } else if (editor_now_ms() < s_msg2_until && doc_current_is_transient()) {
        snprintf(wide, sizeof wide, "%s", UI_OUT_BACK);
    } else {
        if (s_msg[0] != '\0') {
            s_msg[0] = '\0';
        }
        const char *nm = doc_buf_name(doc_buf_current());
        const uint8_t m = kbd_mods();
        char mod[5];
        int mi = 0;
        if (m & KBD_CTRL)     { mod[mi++] = '^'; }
        if (m & KBD_MOD_LALT) { mod[mi++] = 'A'; }
        if (m & KBD_MOD_RALT) { mod[mi++] = 'G'; }
        if (m & KBD_SHIFT)    { mod[mi++] = 'S'; }
        mod[mi] = '\0';
        /* Battery at the right-hand end, as a four-cell bar and nothing else.
         * It is only drawn when the hardware can actually say - see
         * battery.h. A fabricated percentage on an instrument someone is
         * performing with is worse than a blank. */
        char bat[8] = "";
        const int bp = battery_percent();
        if (bp >= 0) {
            const int filled = (bp * 4 + 50) / 100;
            snprintf(bat, sizeof bat, " %c%c%c%c",
                     filled > 0 ? '#' : '.', filled > 1 ? '#' : '.',
                     filled > 2 ? '#' : '.', filled > 3 ? '#' : '.');
        }
        snprintf(wide, sizeof wide, "%-11.11s%c %3d:%-3d %s%s%s%s",
                 nm[0] ? nm : "scratch",
                 doc_dirty() ? '*' : ' ',
                 s_cursor_line + 1, s_cursor_col + 1,
                 mod,
                 kbd_connected() ? "K" : "-",
                 doc_sd_present() ? "S" : "-",
                 bat);
    }
    snprintf(s, sizeof s, "%-*.*s", TEXT_COLS, TEXT_COLS, wide);

    /* THE BAR ITSELF SAYS WHICH KIND OF BUFFER YOU ARE IN.
     *
     * A command with more than one line of output moves you into '+out'. That
     * is deliberate - output is a buffer, not a scrollback - but the move was
     * unannounced: the block above SKIPS the name field entirely while a
     * message is live, and every command sets a message for several seconds.
     * So during the exact window in which you were just teleported, nothing
     * on the screen said where you had landed.
     *
     * The owner hit this. They ran a command, were moved into '+out', tried to
     * run the lines they could see - which were command OUTPUT, formatted with
     * a line-number prefix - and got "not a command" with no explanation.
     *
     * Inverting the whole bar costs no columns, cannot be missed, and does not
     * expire with the message. Dark bar: your document. Light bar: output. */
    const int att = doc_current_is_transient() ? TG_NORMAL : TG_INVERSE;
    for (int c = 0; c < TEXT_COLS; c++) {
        tg_put(c, STATUS_ROW, s[c] ? s[c] : ' ', att);
    }
}

/* The span of the step that is sounding on a lane line, in document offsets:
 * [*from, *to). Returns false when nothing on this line is sounding.
 *
 * WHY OFFSETS AND NOT COLUMNS. A 32-step lane written out is 38 characters
 * against a 30-column grid, so it wraps - and a mark derived from a display
 * row's column would land on the wrong row the moment it did. That is exactly
 * the bug that was fixed once already in current_line(), which read the wrap
 * table instead of the document. Compute in document space, project through
 * the wrap table, never the other way round.
 *
 * THE PLAYHEAD MARKS THE STEP, NOT THE HIT. It reads as one transport sweeping
 * the document rather than lamps blinking independently; it shows where you are
 * in the bar even on a lane that is resting; and it stays truthful under
 * editing, because changing 'x...' to '..x.' changes which steps sound but not
 * where they are.
 *
 * AND A STEP IS A SPAN (docs/MANIFESTO.md §3.6): 'x%15' lights all four
 * characters, a chord lights from its first note to its last. The owner kept the
 * goal - you can always see what is sounding - and dropped the one-character
 * mechanism that was refusing chords. */
static bool playhead_span(int line_off, const char *lbuf, int at, int len,
                          int *from, int *to)
{
    if (!seq_running()) {
        return false;
    }
    /* The lane's name is its CANONICAL address - 'disc:1' is 'disc' - exactly as
     * the lane command stored it, or the mark would miss a lane it is playing. */
    lane_name_t ln;
    if (lane_name_parse(lbuf + at, (size_t)len, &ln) != LN_OK) {
        return false;
    }
    const seq_lane_t *l = seq_lane_find(ln.canon, -1);
    /* Exactly the clock's skip test. If it would not sound, it must not be
     * marked - that makes "the playhead is sweeping this line" and "this lane
     * is sounding" the same statement, which is what the toggle relies on. */
    if (l == NULL || l->muted || l->slots == 0) {
        return false;
    }
    /* The argument, delimited the way the dispatcher delimits it. */
    int a = at + len;
    while (lbuf[a] == ' ' || lbuf[a] == '\t') {
        a++;
    }
    /* A LANE COMPILED FROM TEXT THAT HAS SINCE BEEN EDITED would put the mark on
     * characters that are not the ones sounding. This compared step COUNTS,
     * which an edit that keeps the count - 'x...' to '..x.' - passed; the hash
     * of the text is what the toggle already uses to tell "unchanged" from
     * "edited", so it is exactly the right test here too. */
    if (seq_pattern_hash(lbuf + a) != l->src) {
        return false;
    }
    /* THE LANE'S OWN POSITION, not the global sixteenth. This took
     * seq_position() % steps, so a '/2' lane's mark ran at twice the speed of
     * its sound and a nested lane's at the wrong one entirely. */
    int slot = 0;
    uint32_t cycle = 0;
    if (!seq_lane_now(l, &slot, &cycle)) {
        return false;
    }
    static seq_comp_t comp;             /* the editor task only */
    if (seq_pattern_compile(lbuf + a, &comp) != SEQ_PAT_OK) {
        return false;
    }
    int f = 0, t = 0;
    if (!seq_pattern_mark(&comp, slot, cycle, &f, &t)) {
        return false;
    }
    *from = line_off + a + f;
    *to   = line_off + a + t;
    return true;
}

/* WHAT THE TEXT KEEPS WHEN THE PREVIEW IS UP.
 *
 * viz_pane() decides the rectangle and the direction; these two only subtract
 * it. Keeping the decision in one place matters because the wrap width, the
 * scroll clamp and the draw loop all have to agree - if they disagree by one
 * cell the cursor sits inside the picture and there is no way to tell.
 *
 * THE PREVIEW HAS A BORDER, and it earns the cell it costs twice over. It marks
 * where the picture ends, which the owner asked for; and, because the border is
 * drawn every frame across the pane's full height, the cells below a short
 * frame are written rather than left holding whatever the last layout put
 * there - which is what showed up as static junk in the bottom right. */
static viz_pane_t pane_now(void)
{
    return viz_pane(TEXT_COLS, TEXT_ROWS);
}

/* The split always stacks, so the text keeps every column and gives up rows.
 * Full-width code is the point: a pattern line never wraps at any density. */
static int text_cols_now(void)
{
    return TEXT_COLS;
}

static int text_rows_now(void)
{
    const viz_pane_t p = pane_now();
    return (p.h > 0) ? p.y : TEXT_ROWS;
}

/* Draw the preview: a stroke all the way round, the frame inside it, and every
 * cell of the rectangle written. Called after the text, so the pane owns its
 * area outright and nothing from the code side can bleed into it. */
static void draw_pane(const viz_pane_t *p)
{
    if (p->w <= 0 || p->h <= 0) {
        return;
    }
    const int iw = p->w - 2, ih = p->h - 2;   /* inside the stroke */
    /* Tell the generators how big the picture is. Doing it here, from the
     * geometry that is about to be drawn, is the only way the frame cannot be
     * the wrong shape for its pane. */
    viz_size(iw, ih);

    for (int r = 0; r < p->h; r++) {
        const char *row = (r >= 1 && r <= ih) ? viz_row(r - 1) : NULL;
        const bool edge_row = (r == 0 || r == p->h - 1);
        for (int cc = 0; cc < p->w; cc++) {
            char ch;
            if (edge_row) {
                ch = (cc == 0 || cc == p->w - 1) ? '+' : '-';
            } else if (cc == 0 || cc == p->w - 1) {
                ch = '|';
            } else {
                /* The frame SAMPLED to the pane: the same cell when the two are
                 * one size, the nearest when an output bigger than the panel
                 * is setting the size (viz_out_size). */
                const int vx = cc - 1;
                (void)row;
                ch = viz_cell_fit(vx, r - 1, iw, ih);
            }
            tg_put(p->x + cc, p->y + r, ch, TG_NORMAL);
        }
    }
}

void editor_draw(void)
{
    wrap(text_cols_now());

    /* Recover the top line from the anchored offset, then scroll to keep the
     * cursor on screen, then re-anchor. */
    int top = 0;
    for (int i = 0; i < s_line_count; i++) {
        if (s_line_start[i] <= s_top_offset) {
            top = i;
        } else {
            break;
        }
    }
    if (s_cursor_line < top) {
        top = s_cursor_line;
    }
    const int trows = text_rows_now();
    if (s_cursor_line >= top + trows) {
        top = s_cursor_line - trows + 1;
    }
    if (top < 0) {
        top = 0;
    }
    s_top_offset = s_line_start[top];
    const int s_top_line = top;

    const size_t len = doc_len();
    s_cur_col = s_cur_row = -1;
    s_cur_under = false;

    /* Declared outside the row loop ON PURPOSE: it is computed once per
     * LOGICAL line and must survive across that line's continuation rows, so
     * a wrapped lane keeps its playhead. Every logical-line start resets it. */
    int ph_from = -1, ph_to = -1;

    for (int r = 0; r < trows; r++) {
        const int li = s_top_line + r;
        const int start = (li < s_line_count) ? s_line_start[li] : 0;
        const int end   = (li < s_line_count)
                          ? ((li + 1 < s_line_count) ? s_line_start[li + 1]
                                                     : (int)len)
                          : 0;

        /* Mark a recognised command. Only the display row that BEGINS a
         * logical line can carry the sigil, and only the command word itself
         * is marked - so the eye learns "inverse word = the machine knows
         * this" without a second colour, which a one-bit panel does not
         * have. An unrecognised command is left looking like prose, which is
         * how it will behave. */
        int mark_at = -1, mark_len = 0;
        if (li < s_line_count &&
            (start == 0 || doc_at((size_t)start - 1) == '\n')) {
            char lbuf[128];
            line_at((size_t)start, lbuf, sizeof lbuf);
            ph_from = ph_to = -1;
            if (cmd_recognise(lbuf, &mark_at, &mark_len) == NULL) {
                mark_at = -1;
            } else if (!playhead_span(start, lbuf, mark_at, mark_len,
                                      &ph_from, &ph_to)) {
                ph_from = ph_to = -1;
            }
        } else if (r == 0 && li < s_line_count) {
            /* The top row can be the CONTINUATION of a line that begins above
             * the viewport. Walk back to its start once, so a wrapped lane
             * does not lose its playhead the moment it scrolls. */
            size_t s = (size_t)start;
            while (s > 0 && doc_at(s - 1) != '\n') {
                s--;
            }
            char lbuf[128];
            int a, n;
            line_at(s, lbuf, sizeof lbuf);
            ph_from = ph_to = -1;
            if (cmd_recognise(lbuf, &a, &n) == NULL ||
                !playhead_span((int)s, lbuf, a, n, &ph_from, &ph_to)) {
                ph_from = ph_to = -1;
            }
        }

        const int tc = text_cols_now();
        for (int c = 0; c < tc; c++) {
            char ch = ' ';
            if (li < s_line_count) {
                const int idx = start + c;
                if (idx < end) {
                    const char d = doc_at((size_t)idx);
                    ch = (d == '\n') ? ' ' : d;
                }
            }
            /* The playhead gets its OWN attribute rather than sharing the
             * cursor's solid block. Two solid blocks on a one-ink panel are
             * two things that look identical, and the owner lost their cursor
             * inside a running lane because of it. They are independent bits,
             * so a cursor sitting on the playhead shows as both.
             *
             * Computed BEFORE the cursor capture, because the blink needs to
             * know whether the playhead is passing through the cursor cell. */
            const bool playing = ph_from >= 0 && li < s_line_count &&
                                 (start + c) >= ph_from && (start + c) < ph_to &&
                                 (start + c) < end;
            bool marked = mark_at >= 0 &&
                          c >= mark_at && c < mark_at + mark_len;
            /* THE CHARACTER A PATTERN WAS REFUSED FOR, boxed - a bar above and a
             * bar below, which nothing else on the panel draws - until the next
             * edit. The status bar says why; this says where, so nobody has to
             * count columns at 2 a.m. */
            const bool refused = s_err_off >= 0 && li < s_line_count &&
                                 (start + c) == s_err_off;
            bool under = playing;
            if (refused) {
                under = true;
                marked = true;
            }
            const bool is_cursor = (li == s_cursor_line && c == s_cursor_col);
            if (is_cursor) {
                s_cur_col = c; s_cur_row = r; s_cur_ch = ch;
                s_cur_under = under;
                s_cur_over  = marked;
            }
            /* The cursor keeps the solid block to itself. A recognised
             * command word gets a bar on top instead of sharing it. */
            const bool inv = is_cursor && s_cursor_on;
            tg_put(c, r, ch, cell_attr(inv, under, marked));
        }

        /* Any column the text does not reach is blanked, so a narrower text
         * area cannot leave the previous layout's glyphs standing. */
        for (int c = tc; c < TEXT_COLS; c++) {
            tg_put(c, r, ' ', TG_NORMAL);
        }
    }

    /* The visual, frame by frame, beside the code that makes it - or under it
     * on a narrow grid. The same document holds both, so a pattern line and the
     * picture it produces are inches apart on one screen, which is the entire
     * reason to put it here rather than on a page of its own. */
    {
        const viz_pane_t p = pane_now();
        /* Rows the text gave up are blanked before the pane is drawn, so a
         * shrunken text area leaves nothing behind it either. */
        for (int r = trows; r < TEXT_ROWS; r++) {
            for (int c = 0; c < TEXT_COLS; c++) {
                tg_put(c, r, ' ', TG_NORMAL);
            }
        }
        draw_pane(&p);
    }

    /* Cells first, then sub-cell chrome on top of them. Note that this
     * RENDERS but does not PUSH: the caller pushes once, with editor_present,
     * after the chrome is in the framebuffer too. */
    status_bar();
    /* The CPU side, timed for the heartbeat. It was the budget: 86 us a
     * 12x24 cell with the scheduler held, 94 by this wall clock, 34 ms for a
     * full grid against a 4.75 ms push. The face is pre-turned now (textgrid.c)
     * and a cell is 3.8 us - main.c's bench_render prints both at boot. */
    const int64_t t0 = esp_timer_get_time();
    { const uint32_t n = (uint32_t)tg_render(); s_cells += n; s_cells_total += n; }
    s_render_us += (uint32_t)(esp_timer_get_time() - t0);
}

/* Repaint only the cursor cell. One 12 x 24 cell is 36 bytes on the wire
 * against 15,000 for a frame, so a blink is close to free on the bus.
 *
 * docs/OS.md bans cursor blink outright, on the grounds that a slow panel
 * must never animate. The real cost is not the bus, it is that a blink keeps
 * kicking the panel into HPM and the idle-LPM policy never fires. So the
 * blink is bounded: main stops calling this once typing has paused, the
 * cursor is left solid, and the panel is allowed to drop to 1 Hz.
 */
void editor_blink(bool on)
{
    if (s_cur_col < 0 || on == s_cursor_on) {
        return;
    }
    s_cursor_on = on;
    /* cell_attr, not a second copy of the expression. The copy that used to
     * live here dropped the playhead bit, so a blink erased the bar from the
     * one cell where the cursor and the playhead meet. */
    tg_put(s_cur_col, s_cur_row, s_cur_ch,
           cell_attr(on, s_cur_under, s_cur_over));
    tg_render();
}

/* Push whatever editor_draw/editor_blink put in the framebuffer.
 *
 * This exists because the alternative was a silent no-op. tg_flush() renders
 * AND pushes, but editor_draw has already rendered - so tg_flush saw zero
 * dirty cells, concluded there was nothing to send, and skipped the SPI push
 * entirely. Every edit was drawn perfectly into the framebuffer and never
 * reached the glass. Splitting render from present makes that mistake
 * impossible to make again by accident. */
void editor_present(size_t *bytes)
{
    size_t n = 0;
    st7305_flush(&n);
    if (bytes != NULL) {
        *bytes = n;
    }
    /* Counted, not logged. A capped one-shot probe went quiet after 24 pushes
     * and made a perfectly healthy device look hung - the screen had stopped
     * blinking by design at the same moment, so both signals died together.
     * The heartbeat reports these instead, so quiet always means idle and
     * never means broken. */
    if (n > 0) {
        s_pushes++;
        s_push_bytes += n;
    }
}

void editor_cursor_solid(void)
{
    editor_blink(true);
}

/* Move the cursor to a display line and column, preserving the column where
 * the target line is long enough. This needs the wrap table, so it is rebuilt
 * first - the table from the last draw is stale the moment anything is
 * inserted. */
/* Callers wrap first; this does not, because an arrow press was walking the
 * gap buffer up to three times per keystroke. */
static void goto_line_col(int line, int want_col)
{
    if (line < 0) {
        line = 0;
    }
    if (line >= s_line_count) {
        line = s_line_count - 1;
    }
    const int start = s_line_start[line];
    const int end   = (line + 1 < s_line_count)
                      ? s_line_start[line + 1] : (int)doc_len();
    int width = end - start;
    /* A hard newline is part of the line but not a column you can sit past. */
    while (width > 0 && doc_at((size_t)(start + width - 1)) == '\n') {
        width--;
    }
    int col = want_col;
    if (col > width) {
        col = width;
    }
    doc_move_to((size_t)(start + col));
}

static void line_bounds(int *start, int *end)
{
    const int line = s_cursor_line;
    *start = s_line_start[line];
    *end   = (line + 1 < s_line_count)
             ? s_line_start[line + 1] : (int)doc_len();
    while (*end > *start && doc_at((size_t)(*end - 1)) == '\n') {
        (*end)--;
    }
}

static bool is_word_char(char c)
{
    return (c >= 'a' && c <= 'z') || (c >= 'A' && c <= 'Z') ||
           (c >= '0' && c <= '9') || c == '_';
}

static void move_vertical(int delta)
{
    if (s_goal_col < 0) {
        s_goal_col = s_cursor_col;
    }
    goto_line_col(s_cursor_line + delta, s_goal_col);
}

/* Ctrl chords. Chosen from readline rather than invented, because they are
 * already in a lot of people's fingers and cost no new keys on a thumb
 * keyboard - docs/OS.md is explicit that one held modifier plus one letter is
 * the ceiling for a thumb. */
static void handle_ctrl(char c)
{
    switch (c) {
    case 'g': {
        /* Jump to the guide. Everything is reachable by name, but reaching
         * the place where names are typed cannot itself require typing a
         * name - that circle has to be broken by a gesture. */
        for (int i = 0; i < DOC_MAX_BUFFERS; i++) {
            if (strcmp(doc_buf_name(i), "guide") == 0) {
                doc_buf_select(i);
                doc_move_to(0);
                s_goal_col = -1;
                s_top_offset = 0;
                editor_invalidate();
                tg_invalidate();
                snprintf(s_msg, sizeof s_msg, "%s", UI_GUIDE_HINT);
                s_msg_until = editor_now_ms() + 4000;
                return;
            }
        }
        snprintf(s_msg, sizeof s_msg, "%s", UI_NO_GUIDE);
        s_msg_until = editor_now_ms() + 3000;
        return;
    }
    case 'o': {
        /* A toggle, not a jump. From anywhere it shows the output; from the
         * output it returns you to what you were writing. */
        const int here = doc_buf_current();
        int target;
        if (strcmp(doc_buf_name(here), "+out") == 0 && s_prev_buf >= 0) {
            target = s_prev_buf;
        } else {
            target = doc_buf_find("+out");
        }
        if (target >= 0 && target != here && doc_buf_select(target) == ESP_OK) {
            s_prev_buf = here;
            editor_invalidate();
            tg_invalidate();
            const char *nm = doc_buf_name(target);
            snprintf(s_msg, sizeof s_msg, "%s", nm[0] ? nm : "scratch");
            s_msg_until = editor_now_ms() + 2500;
        }
        return;
    }
    /* DOCUMENT SWITCHING WITHOUT A MODE.
     *
     * The owner could not see what documents existed without '>list', which
     * moved them somewhere else and left them stranded. Two keys walk the
     * open documents in place: no list to enter, no mode to leave, and the
     * status bar already names where you are. This is cmd-tab, not a file
     * browser - the browser is what "no menu diving" rules out.
     *
     * '+' buffers are skipped. Machine output is not somewhere you navigate
     * TO; it is somewhere a command puts you, and Ctrl-O brings you back. */
    case 'l': cycle_buffer(+1); break;
    case 'j': cycle_buffer(-1); break;

    case 'z': doc_undo(); break;
    case 'y': doc_redo(); break;
    case 'a': { int s, e; line_bounds(&s, &e); doc_move_to((size_t)s); break; }
    case 'e': { int s, e; line_bounds(&s, &e); doc_move_to((size_t)e); break; }
    case 'b': doc_left();  break;
    case 'f': doc_right(); break;
    case 'p': move_vertical(-1); break;
    case 'n': move_vertical(+1); break;
    case 'k': {                      /* kill to end of line */
        int s, e;
        line_bounds(&s, &e);
        const size_t cur = doc_cursor();
        doc_move_to((size_t)e);
        while (doc_cursor() > cur) {
            doc_backspace();
        }
        break;
    }
    case 'w': {                      /* delete the word before the cursor */
        while (doc_cursor() > 0 && !is_word_char(doc_at(doc_cursor() - 1))) {
            doc_backspace();
        }
        while (doc_cursor() > 0 && is_word_char(doc_at(doc_cursor() - 1))) {
            doc_backspace();
        }
        break;
    }
    default: break;
    }
}

/* Motion is logged so navigation can be checked from the bench without
 * anyone having to read the panel over someone's shoulder. */
#ifndef EDITOR_TRACE_MOTION
#define EDITOR_TRACE_MOTION 0
#endif

/* Off by default. Each line costs the USB-serial VFS a mutex take and a
 * ring-buffer send PER CHARACTER, which is real latency on the keystroke path
 * for a trace nobody is reading during normal use. */
static void log_motion(const char *what)
{
#if EDITOR_TRACE_MOTION
    /* Re-wrap before reporting. editor_handle wraps once up front, so by the
     * time a motion has run the cached line/col describe where the cursor
     * WAS - which made a working goal column look broken in the trace while
     * the offsets proved it correct. Only compiled in for tracing, so the
     * extra wrap costs nothing in a normal build. */
    wrap(text_cols_now());
    ESP_LOGI("editor", "%s -> line %d col %d (offset %u of %u)",
             what, s_cursor_line + 1, s_cursor_col + 1,
             (unsigned)doc_cursor(), (unsigned)doc_len());
#else
    (void)what;
#endif
}

/* Copy the logical line that begins at `from`. */
static void line_at(size_t from, char *out, size_t max)
{
    const size_t len = doc_len();
    size_t n = 0;
    for (size_t i = from; i < len && n + 1 < max; i++) {
        const char ch = doc_at(i);
        if (ch == '\n') {
            break;
        }
        out[n++] = ch;
    }
    out[n] = '\0';
}

/* Copy the LOGICAL line the cursor is on - the run between newlines in the
 * document, not the run between soft wraps on the screen.
 *
 * This used the wrap table, and a command longer than thirty columns was
 * therefore cut at the wrap and its PREFIX executed, silently:
 * ">name Rust Belt Lullaby and the" filed the document as "Rust Belt Lullaby
 * and". No error, no mark, wrong name in the archive. It is the same class of
 * defect as the trailing-whitespace trap docs/SUBSTRATE.md is proud of
 * engineering out of existence - destructive, silent, discovered later - and
 * every MIDI command in the brief is long enough to hit it.
 *
 * A logical line also means a wrapped command runs identically from any of
 * its display rows, which removes the confusing "not a command" error when
 * standing on a continuation row. */
static void current_line(char *out, size_t max)
{
    const size_t len = doc_len();
    size_t s = doc_cursor();
    if (s > len) {
        s = len;
    }
    while (s > 0 && doc_at(s - 1) != '\n') {
        s--;
    }
    size_t n = 0;
    for (size_t i = s; i < len && n + 1 < max; i++) {
        const char ch = doc_at(i);
        if (ch == '\n') {
            break;
        }
        out[n++] = ch;
    }
    out[n] = '\0';
}

/* The Run verb from docs/SUBSTRATE.md. In a guide buffer this will be plain
 * Enter; until buffer kinds exist, Ctrl+Enter runs the line under the cursor
 * from anywhere, which is the same gesture without the mode. */
/* Walk to the next or previous real document, skipping machine buffers and
 * empty slots. Wraps. */
static void cycle_buffer(int dir)
{
    const int n = DOC_MAX_BUFFERS;
    const int here = doc_buf_current();
    for (int step = 1; step <= n; step++) {
        const int i = ((here + dir * step) % n + n) % n;
        const char *nm = doc_buf_name(i);
        if (nm == NULL || nm[0] == '+') {
            continue;
        }
        if (doc_buf_select(i) == ESP_OK) {
            s_top_offset = 0;
            s_goal_col = -1;
            doc_move_to(0);
            snprintf(s_msg, sizeof s_msg, "%s", nm[0] ? nm : "scratch");
            s_msg_until = editor_now_ms() + 1500;
            editor_invalidate();
            tg_invalidate();
            return;
        }
    }
    snprintf(s_msg, sizeof s_msg, "only one document");
    s_msg_until = editor_now_ms() + 1500;
}

/* Cut the line under the cursor - the whole line, not the display line -
 * from column `col` to its end. */
static void cut_line_from(int col)
{
    const size_t len = doc_len();
    size_t s = doc_cursor();
    if (s > len) {
        s = len;
    }
    while (s > 0 && doc_at(s - 1) != '\n') {
        s--;
    }
    size_t e = s;
    while (e < len && doc_at(e) != '\n') {
        e++;
    }
    const size_t from = s + (size_t)col;
    if (from >= e) {
        return;
    }
    doc_move_to(e);
    for (size_t i = e; i > from; i--) {
        doc_backspace();
    }
}

/* Move the view to '+out' at `from`, where a command's lines begin. False
 * when there is no '+out' or the view is already there. */
static bool show_output(size_t from, const char *msg)
{
    const int out = doc_buf_find("+out");
    const int here = doc_buf_current();
    if (out < 0 || out == here || doc_buf_select(out) != ESP_OK) {
        return false;
    }
    s_prev_buf = here;
    doc_move_to(from);
    s_top_offset = (int)from;
    s_goal_col = -1;
    /* SAY HOW TO GET BACK, AND SAY IT LAST.
     *
     * The command's own result is shown first, then the way out, so
     * the owner reads the answer and then learns the exit. The owner
     * ran a command, was moved here, and "had no idea how to get
     * back" - so they ran another command, which piled onto the same
     * page. Ctrl-O was always the answer and nothing ever said so.
     *
     * Longer than a normal message because it is teaching, not
     * reporting, and it only appears when the view actually moved. */
    snprintf(s_msg, sizeof s_msg, "%s", msg[0] ? msg : "output");
    s_msg_until = editor_now_ms() + 2200;
    s_msg2_until = editor_now_ms() + 5200;
    editor_invalidate();
    tg_invalidate();
    return true;
}

void editor_show_output(size_t from, const char *msg)
{
    if (!show_output(from, msg)) {
        editor_message(msg);
        editor_invalidate();
    }
}

static void run_current_line(void)
{
    char line[128];
    current_line(line, sizeof line);

    const char *p = line;
    while (*p == ' ' || *p == '\t') {
        p++;
    }
    if (*p != '>') {
        snprintf(s_msg, sizeof s_msg, "%s", UI_NOT_A_COMMAND);
        s_msg_until = editor_now_ms() + 3000;
        return;
    }

    /* Where the output buffer ended BEFORE the command, so the view can land
     * on the first line this command wrote rather than the last line of
     * everything ever written. `help` was scrolling to the bottom and hiding
     * its own first three entries with nothing to say so. */
    const int outb = doc_buf_find("+out");
    const size_t out_was = outb >= 0 ? doc_buf_len(outb) : 0;

    char msg[96] = "";
    cmd_run_line(line, CMD_BY_HANDS, msg, sizeof msg);
    /* A PASSWORD TYPED ON THE LINE, the old way, is cut before anything can
     * save it: the command refused it and said where it starts. */
    if (cmd_last_secret_col() >= 0) {
        cut_line_from(cmd_last_secret_col());
    }
    const int lines = cmd_last_output_lines();
    {
        /* Only when the view stays here: a result long enough to move to
         * '+out' would otherwise box a character of the output page. */
        const int col = (lines > 1) ? -1 : cmd_last_error_col();
        if (col >= 0) {
            size_t ls = doc_cursor();
            while (ls > 0 && doc_at(ls - 1) != '\n') {
                ls--;
            }
            s_err_off = (int)ls + col;
        }
    }

    /* A result of more than one line shows itself. Reporting "10 commands" at
     * the bottom of the screen and leaving the actual answer somewhere the
     * owner has to know to look for is not minimalism, it is hiding. */
    if (lines > 1 && show_output(out_was, msg)) {
        return;
    }
    snprintf(s_msg, sizeof s_msg, "%s", msg[0] ? msg : "ok");
    s_msg_until = editor_now_ms() + 4000;
    editor_invalidate();
    tg_invalidate();
}

void editor_handle(const kbd_event_t *ev)
{
    /* One wrap per event. Everything below reads the table; nothing below
     * rebuilds it. */
    wrap(text_cols_now());

    /* A SECRET BEING TYPED TAKES EVERY KEY - ask.h. Enter hands it to the
     * command that asked, Esc takes it back, and either way it is wiped. */
    if (s_ask.active) {
        const int r = ask_feed(&s_ask, ev);
        if (r != ASK_KEEP) {
            const cmd_secret_fn fn = s_ask_fn;
            s_ask_fn = NULL;
            char msg[64] = "";
            if (r == ASK_SUBMIT && fn != NULL) {
                fn(s_ask.buf, msg, sizeof msg);
            }
            ask_end(&s_ask);
            snprintf(s_msg, sizeof s_msg, "%s", r != ASK_SUBMIT
                     ? "stopped - nothing sent" : msg[0] ? msg : "ok");
            s_msg_until = editor_now_ms() + 4000;
        }
        editor_invalidate();
        return;
    }

    /* Any motion that is not vertical, and any edit, drops the goal column. */
    switch (ev->type) {
    case KBD_EV_UP:
    case KBD_EV_DOWN:
        break;
    default:
        s_goal_col = -1;
        break;
    }

    /* Anything but pure motion forgets the refused-character mark: an edit may
     * have fixed it or moved it, a switch leaves its document, and a run sets
     * its own. Motion keeps it, so the cursor can be walked onto it. */
    {
        const bool motion =
            ev->type == KBD_EV_LEFT || ev->type == KBD_EV_RIGHT ||
            ev->type == KBD_EV_UP || ev->type == KBD_EV_DOWN ||
            ev->type == KBD_EV_HOME || ev->type == KBD_EV_END ||
            (ev->type == KBD_EV_CHAR && (ev->mods & KBD_COMMAND_MODS) &&
             (ev->ch == 'a' || ev->ch == 'e' || ev->ch == 'b' || ev->ch == 'f' ||
              ev->ch == 'p' || ev->ch == 'n'));
        if (!motion && s_err_off >= 0) {
            s_err_off = -1;
            editor_invalidate();
        }
    }

    if (ev->type == KBD_EV_ENTER && (ev->mods & KBD_COMMAND_MODS)) {
        run_current_line();
        return;
    }

    if (ev->type == KBD_EV_CHAR && (ev->mods & KBD_COMMAND_MODS)) {
        handle_ctrl((char)(ev->ch >= 'A' && ev->ch <= 'Z'
                           ? ev->ch - 'A' + 'a' : ev->ch));
        return;
    }

    switch (ev->type) {
    case KBD_EV_CHAR:      doc_insert(ev->ch); break;
    case KBD_EV_ENTER:
        /* Enter ALWAYS inserts a newline. Always, in every buffer.
         *
         * It used to run the line in a guide buffer, which is what
         * docs/SUBSTRATE.md describes - and it made the guide uneditable:
         * standing at the end of a command with no way to add a line after
         * it, because the key that adds lines was busy running things. An
         * editor whose Enter key sometimes does not insert a line is not an
         * editor.
         *
         * The sigil made the kind redundant here anyway. A command is marked
         * by '>' in the text, so the machine can tell a command from prose
         * without a mode; the only remaining question is WHEN to run one, and
         * that is a modifier, not a property of the buffer. */
        doc_insert('\n');
        break;
    case KBD_EV_TAB:       doc_insert(' '); doc_insert(' '); break;
    case KBD_EV_BACKSPACE: doc_backspace();   break;
    case KBD_EV_LEFT:      doc_left();  log_motion("left");  break;
    case KBD_EV_RIGHT:     doc_right(); log_motion("right"); break;
    case KBD_EV_UP:        move_vertical(-1); log_motion("up");    break;
    case KBD_EV_DOWN:      move_vertical(+1); log_motion("down");  break;
    case KBD_EV_HOME: { int s, e; line_bounds(&s, &e); doc_move_to((size_t)s); break; }
    case KBD_EV_END:  { int s, e; line_bounds(&s, &e); doc_move_to((size_t)e); break; }
    default: break;
    }
}
