kylebsmith/ESP32-S3-RLCD-cYbErDeCk/firmware/main/vitals.c

#include "vitals.h"
#include "vitals_verdict.h"

#include <stdio.h>
#include <string.h>

#include "esp_heap_caps.h"
#include "esp_log.h"
#include "esp_system.h"
#include "esp_timer.h"
#include "nvs.h"

static const char *TAG = "vitals";

#define NVS_NS   "deck"
#define NVS_KEY  "vitals"
#define WRITE_EVERY_S 60

static vitals_t s_prev;
static uint32_t s_loops;
static int64_t  s_last_write_us;
static char     s_line[VITALS_LINES][VITALS_COLS];
static int      s_nlines;

static void write_record(bool usb_mode, bool running, uint32_t ticks,
                         bool deliberate)
{
    const vitals_t v = {
        .uptime_s     = (uint32_t)(esp_timer_get_time() / 1000000),
        .loops        = s_loops,
        .ticks        = ticks,
        .heap_free    = (uint32_t)heap_caps_get_free_size(MALLOC_CAP_INTERNAL),
        .usb_mode     = usb_mode ? 1u : 0u,
        .running      = running ? 1u : 0u,
        .reset_reason = (uint8_t)esp_reset_reason(),
        .valid        = 1u,
        .deliberate   = deliberate ? 1u : 0u,
    };
    nvs_handle_t h;
    if (nvs_open(NVS_NS, NVS_READWRITE, &h) != ESP_OK) {
        return;
    }
    /* No nvs_commit() error handling and no retry: this is a diagnostic, and a
     * diagnostic that can fail the thing it is diagnosing is worse than no
     * diagnostic. A lost record costs one minute of resolution. */
    if (nvs_set_blob(h, NVS_KEY, &v, sizeof v) == ESP_OK) {
        nvs_commit(h);
    }
    nvs_close(h);
}

void vitals_begin(void)
{
    nvs_handle_t h;
    size_t len = sizeof s_prev;
    if (nvs_open(NVS_NS, NVS_READONLY, &h) == ESP_OK) {
        if (nvs_get_blob(h, NVS_KEY, &s_prev, &len) != ESP_OK ||
            len != sizeof s_prev) {
            memset(&s_prev, 0, sizeof s_prev);
        }
        nvs_close(h);
    }
    s_last_write_us = esp_timer_get_time();

    const esp_reset_reason_t now = esp_reset_reason();
    s_nlines = vitals_verdict(&s_prev, now == ESP_RST_POWERON, s_line,
                              VITALS_LINES);
    for (int i = 0; i < s_nlines; i++) {
        ESP_LOGW(TAG, "%s", s_line[i]);
    }
    if (s_prev.valid) {
        ESP_LOGW(TAG, "  ticks %u, reset then %d, now %d",
                 (unsigned)s_prev.ticks, (int)s_prev.reset_reason, (int)now);
    }
}

void vitals_started(bool usb_mode)
{
    /* A mark that this run began, and in which mode - read by the next boot so
     * a run that wrote nothing else is not described by an older one. One
     * write a boot. */
    write_record(usb_mode, false, 0, false);
}

const vitals_t *vitals_previous(void) { return &s_prev; }

void vitals_loop(bool usb_mode, bool running, uint32_t ticks)
{
    s_loops++;
    if (!usb_mode) {
        /* Serial mode has never shown the bug, so it pays nothing. */
        return;
    }
    const int64_t now = esp_timer_get_time();
    if (now - s_last_write_us < (int64_t)WRITE_EVERY_S * 1000000) {
        return;
    }
    s_last_write_us = now;
    write_record(usb_mode, running, ticks, false);
}

void vitals_goodbye(bool usb_mode, bool running, uint32_t ticks)
{
    write_record(usb_mode, running, ticks, true);
}

int vitals_report(const char *out[VITALS_LINES])
{
    for (int i = 0; i < s_nlines; i++) {
        out[i] = s_line[i];
    }
    return s_nlines;
}
