kylebsmith/ESP32-S3-RLCD-cYbErDeCk/firmware/main/serialkbd.c

/*
 * A keyboard over the USB cable.
 *
 * Two reasons this exists, and the second is the one that matters tonight:
 *
 *  1. It is a real fallback. If no keyboard is paired - or the BLE keyboard is
 *     flat, or lost - the deck is still usable from any terminal over the same
 *     cable that flashes it.
 *  2. It makes the editor testable with no radio at all. Without it, the gap
 *     buffer, the wrap, the cursor, the autosave and the redraw path have no
 *     key source and cannot be exercised on the bench.
 *
 * Input goes through the same queue as BLE HID, so there is exactly one input
 * path and one event taxonomy, per docs/OS.md.
 */
#include "serialkbd.h"

#include "driver/usb_serial_jtag.h"
#include "driver/usb_serial_jtag_vfs.h"
#include "esp_log.h"
#include "freertos/FreeRTOS.h"
#include "freertos/task.h"
#include "kbd.h"
#include "serialkbd_map.h"

static const char *TAG = "serialkbd";


/* A terminal sends Ctrl-A..Ctrl-Z as bytes 1..26. Turning them back into a
 * character plus a modifier means the serial keyboard reaches the same chords
 * as the BLE one, through the same event taxonomy - so undo is testable over
 * the cable and usable when no keyboard is paired. */

static void serial_task(void *arg)
{
    (void)arg;
    uint8_t b;
    skb_state_t st = { 0 };

    while (1) {
        const int n = usb_serial_jtag_read_bytes(&b, 1, portMAX_DELAY);
        if (n <= 0) {
            continue;
        }
        const skb_ev_t e = skb_feed(&st, b);
        if (e.emit) {
            const kbd_event_t ev = { .type = (kbd_ev_type_t)e.type,
                                     .ch = e.ch, .mods = e.mods,
                                     .repeat = false };
            kbd_inject(&ev);
        }
    }
}

esp_err_t serialkbd_init(void)
{
    usb_serial_jtag_driver_config_t cfg = USB_SERIAL_JTAG_DRIVER_CONFIG_DEFAULT();
    cfg.rx_buffer_size = 256;
    /* Room for two of the view's frames (1,436 bytes each, view.c) and the log
     * around them, so a frame is copied in and the editor carries on. At 1024
     * no frame fitted, and every one blocked the editor's loop until USB had
     * drained it. Under 4096, so malloc keeps it in internal RAM. */
    cfg.tx_buffer_size = 4000;

    const esp_err_t err = usb_serial_jtag_driver_install(&cfg);
    if (err != ESP_OK) {
        ESP_LOGW(TAG, "driver install failed: %s", esp_err_to_name(err));
        return err;
    }
    /* Route the console through the driver too, so logging keeps working now
     * that the peripheral has an owner. */
    usb_serial_jtag_vfs_use_driver();

    xTaskCreate(serial_task, "serialkbd", 3072, NULL, 5, NULL);
    ESP_LOGI(TAG, "typing over USB is live - this terminal is a keyboard");
    return ESP_OK;
}
